griswaldbrooks/woodbike-shed/blender/renders/cam_back_right.png

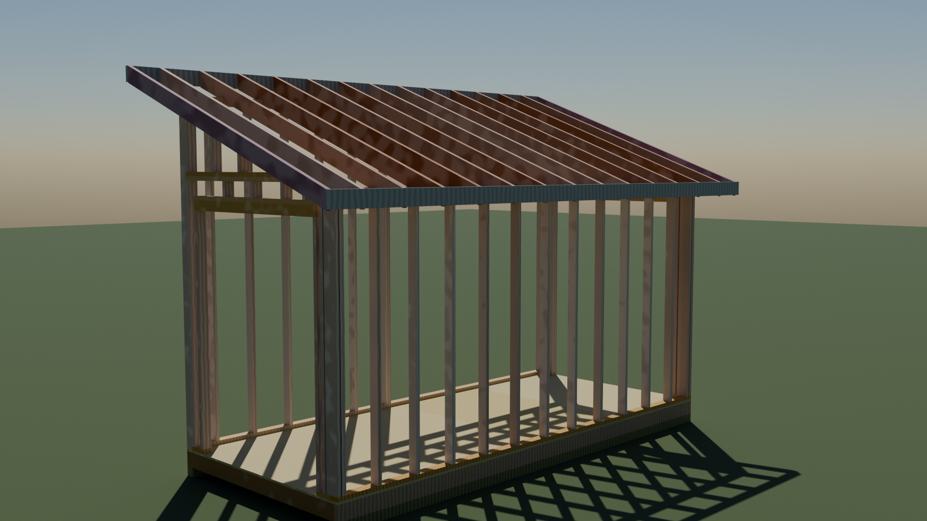
blender/renders/cam_back_right.png
