griswaldbrooks/woodbike-shed/blender/renders/cam_elevation.png

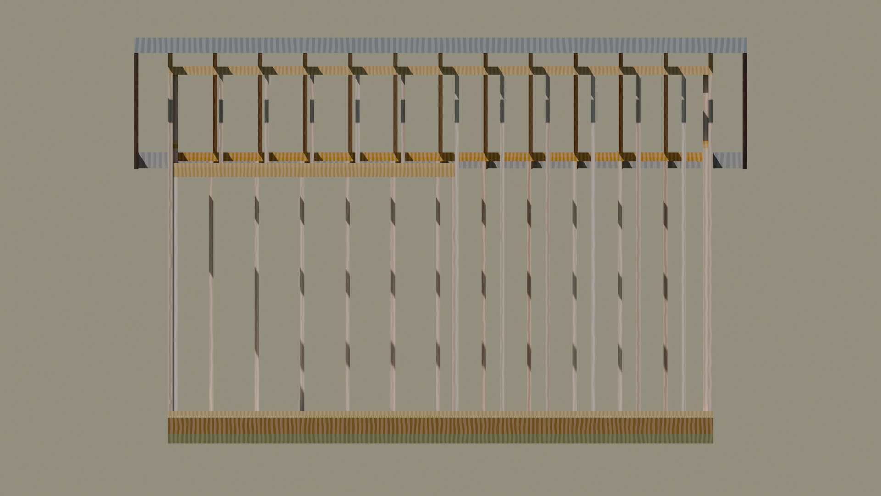
blender/renders/cam_elevation.png
