griswaldbrooks/woodbike-shed/blender/renders/cam_front_left.png

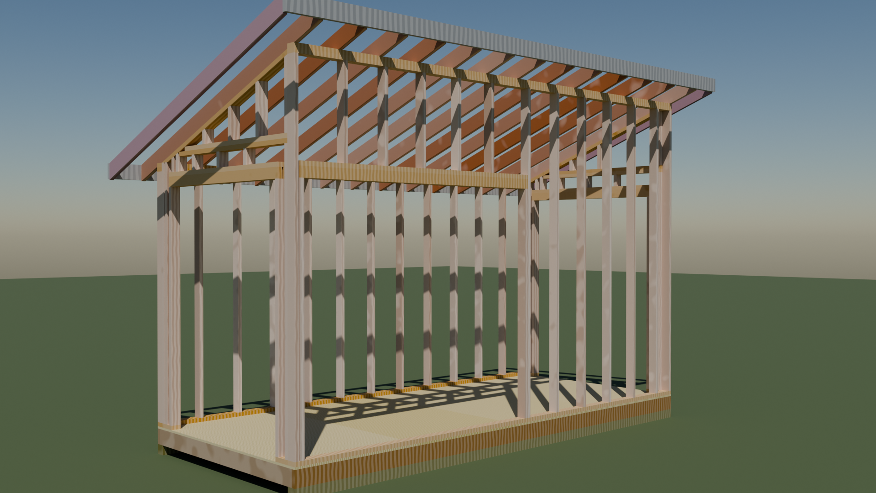
blender/renders/cam_front_left.png
