griswaldbrooks/woodbike-shed/blender/renders/skin/skin_back_right.png

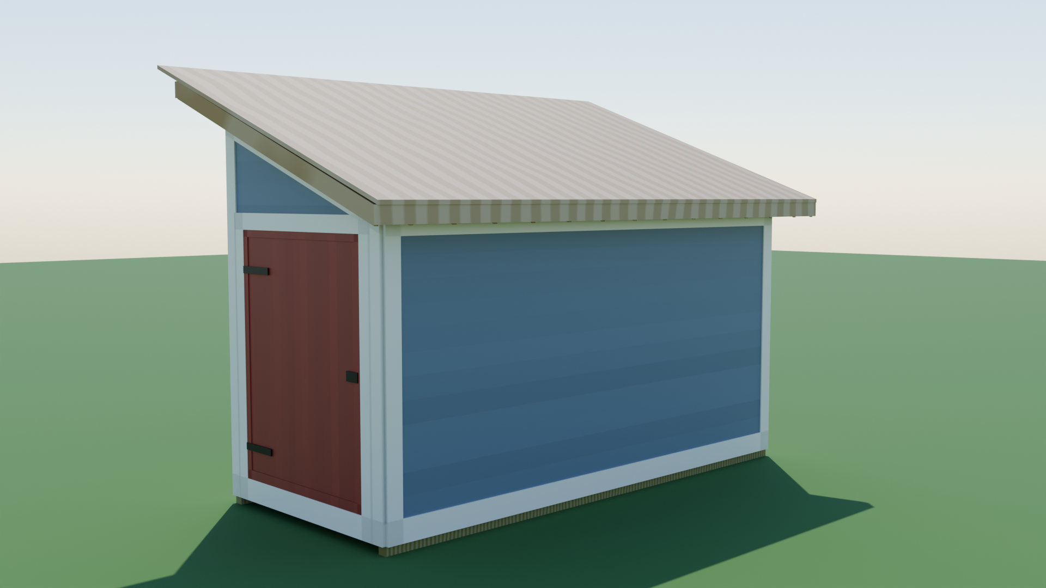
blender/renders/skin/skin_back_right.png
