griswaldbrooks/woodbike-shed/renders/shed-iso-back.png

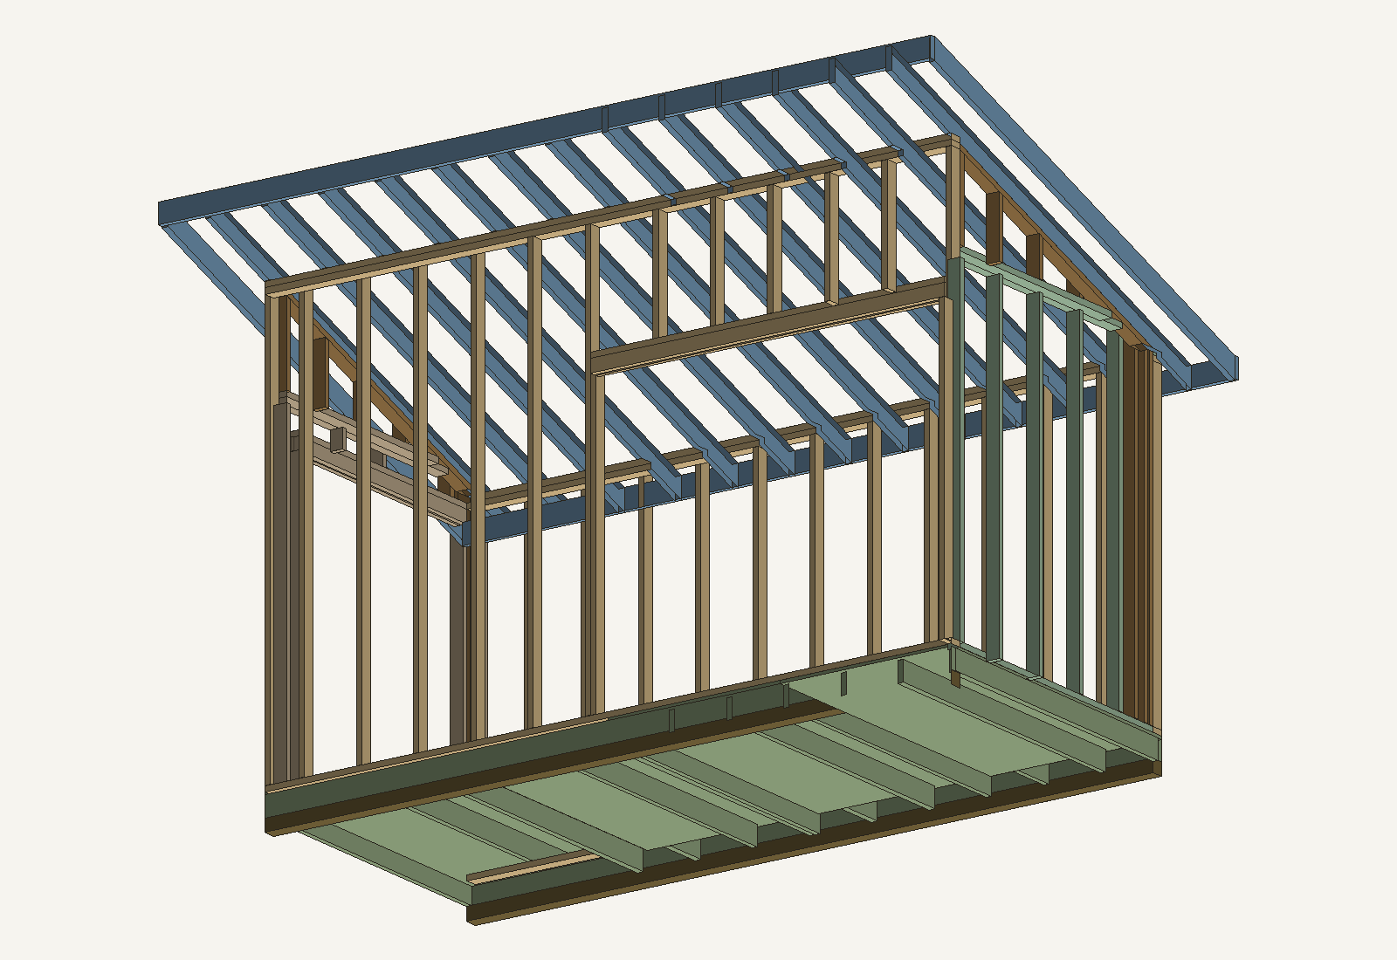
renders/shed-iso-back.png
