griswaldbrooks/woodbike-shed/renders/shed-side-right.png

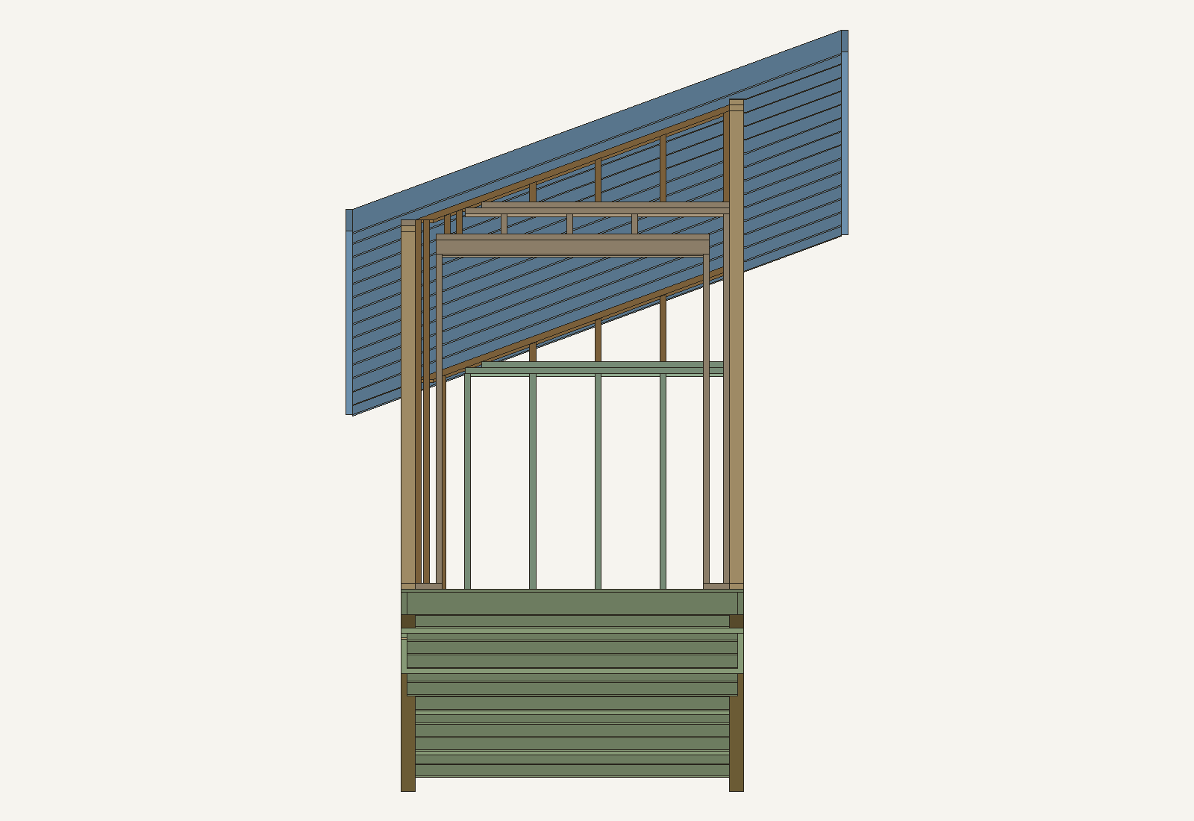
renders/shed-side-right.png
