griswaldbrooks/woodbike-shed/scripts/iso-winner2.png

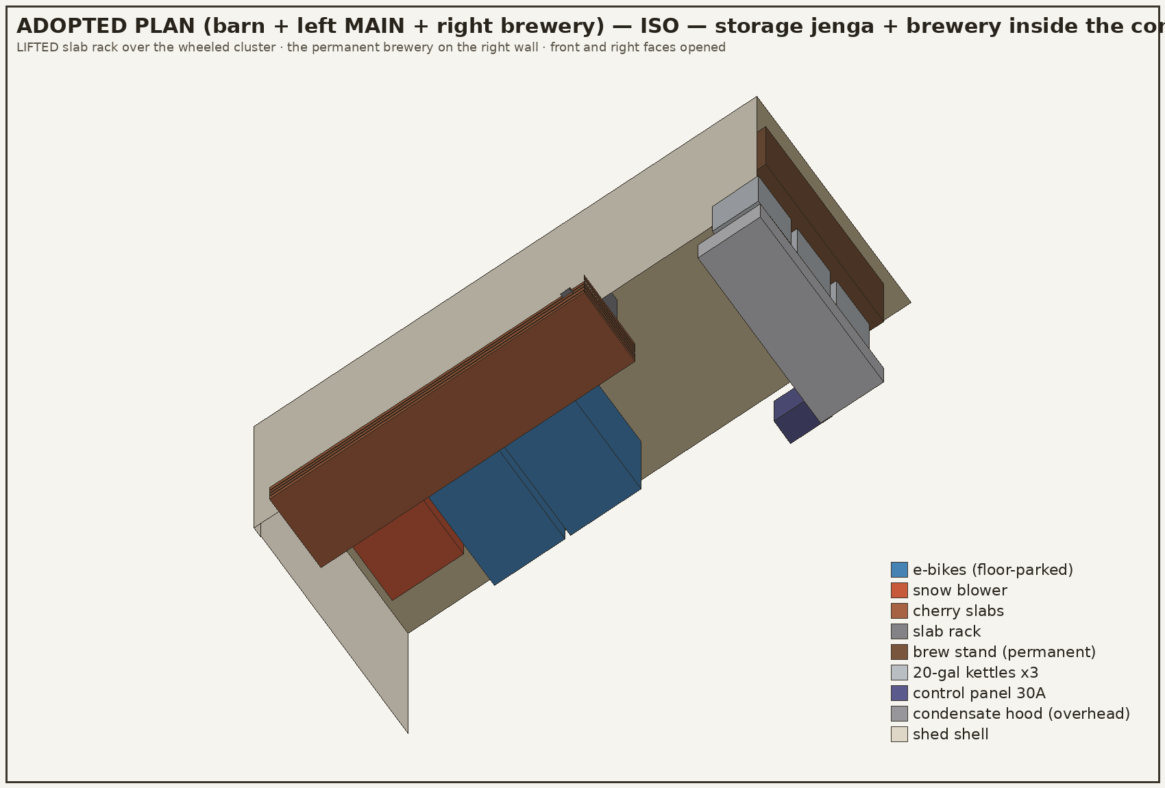
scripts/iso-winner2.png
