griswaldbrooks/woodbike-shed/scripts/plan-winner2.png

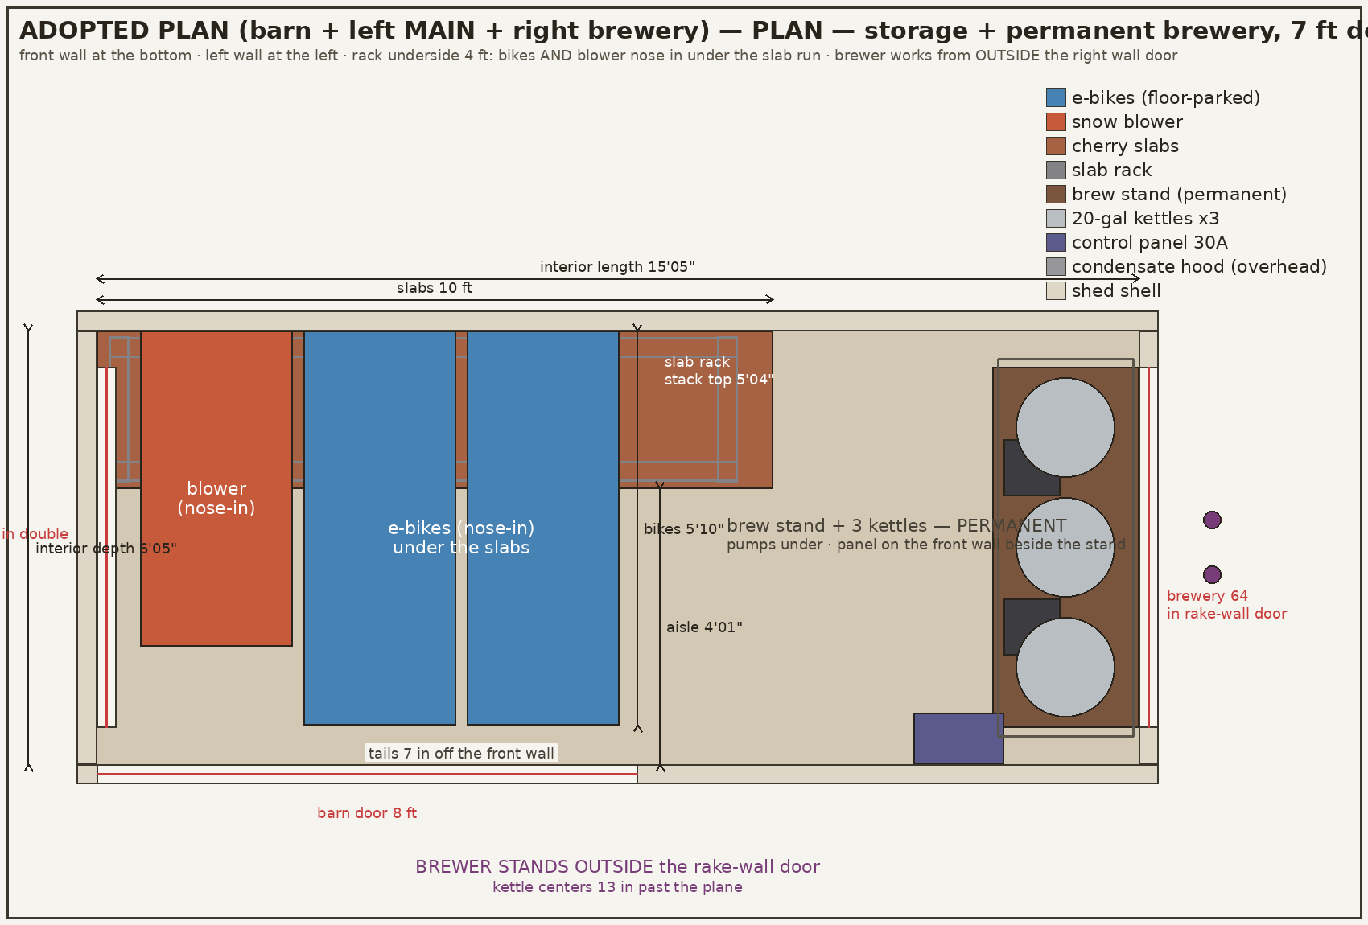
scripts/plan-winner2.png
