griswaldbrooks/woodbike-shed/scripts/section-winner2.png

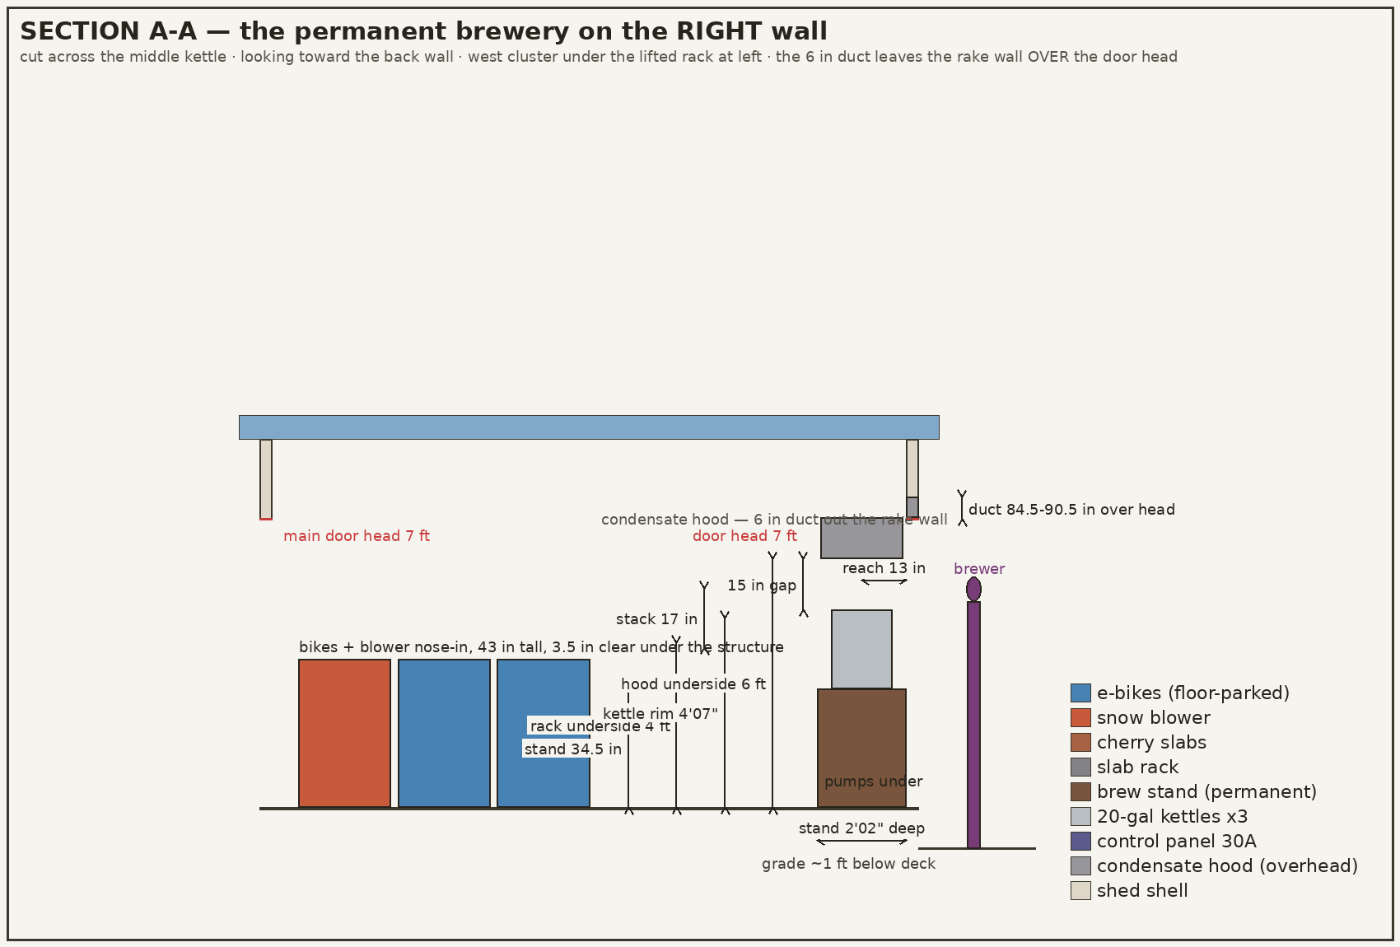
scripts/section-winner2.png
