griswaldbrooks/woodbike-shed/step/059 back wall double top plate short.step

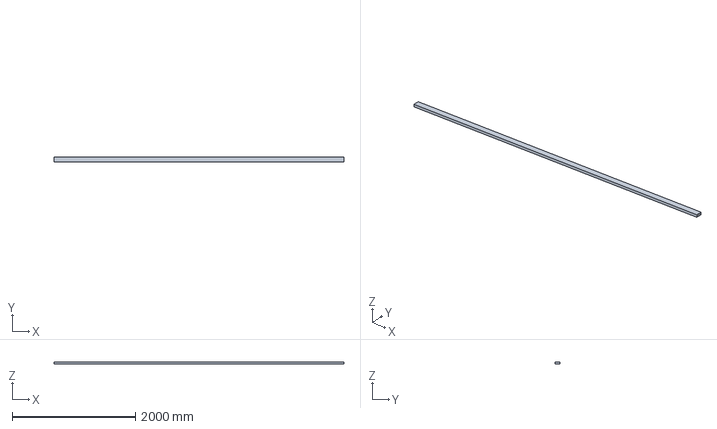
[picture p21: CAD file, 2026-08-24]
step/059 back wall double top plate short.step
4699.0 x 88.9 x 38.1 mm
