griswaldbrooks/woodbike-shed/step/054 back wall studs.step

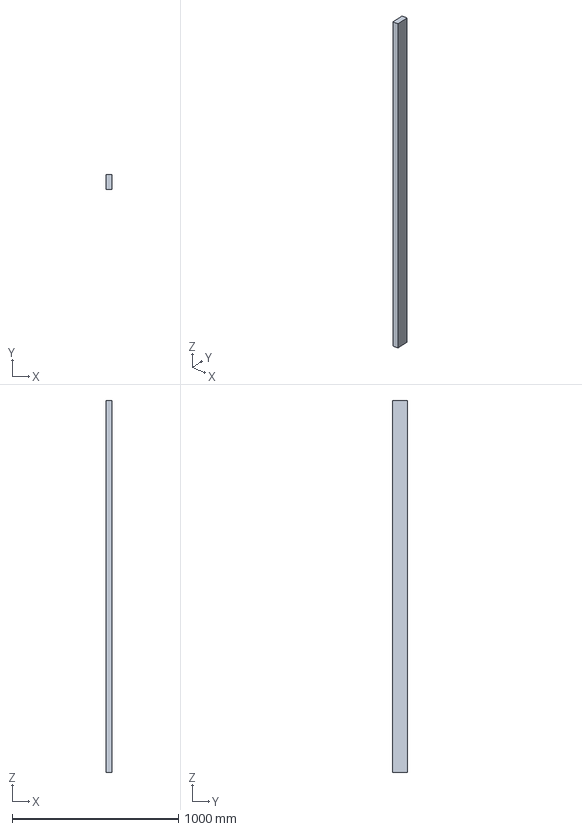
[picture p22: CAD file, 2026-08-24]
step/054 back wall studs.step
38.1 x 88.9 x 2238.4 mm
