griswaldbrooks/woodbike-shed/step/013 floor joist.step

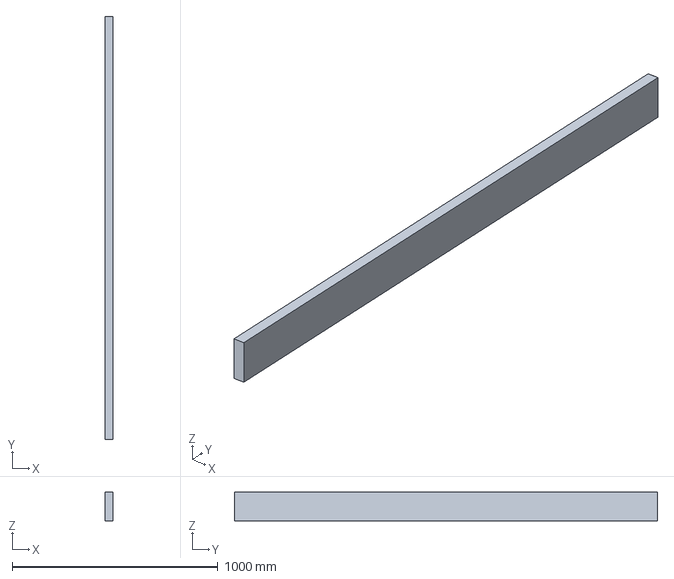
[picture p23: CAD file, 2026-08-24]
step/013 floor joist.step
38.1 x 2057.4 x 139.7 mm
