griswaldbrooks/woodbike-shed/step/275 finish door rails.step

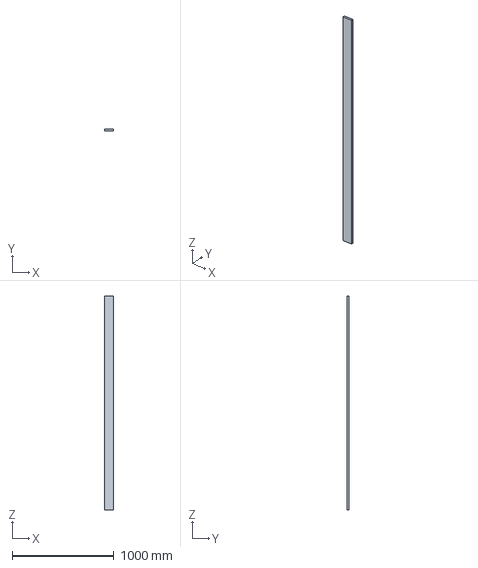
[picture p24: CAD file, 2026-08-24]
step/275 finish door rails.step
88.9 x 19.1 x 2101.8 mm
