griswaldbrooks/woodbike-shed/step/040 front wall cripple studs.step

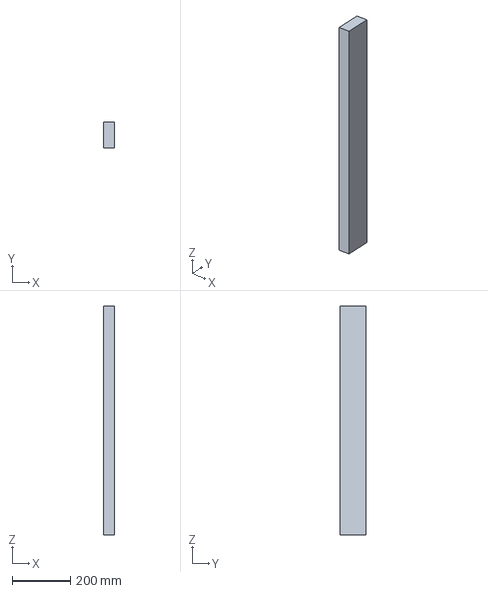
[picture p25: CAD file, 2026-08-24]
step/040 front wall cripple studs.step
38.1 x 88.9 x 787.4 mm
