griswaldbrooks/woodbike-shed/step/037 front wall headers.step

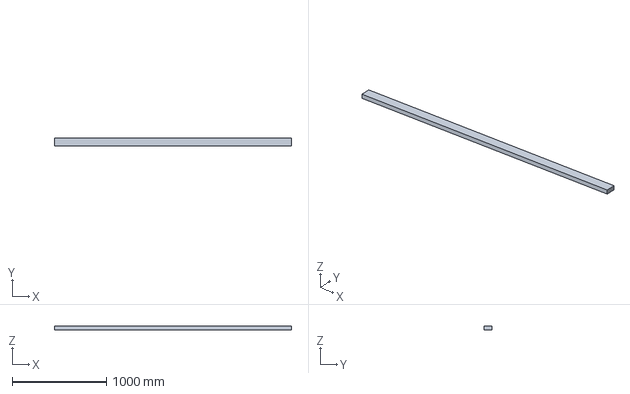
[picture p26: CAD file, 2026-08-24]
step/037 front wall headers.step
2514.6 x 88.9 x 38.1 mm
