griswaldbrooks/woodbike-shed/step/128 finish siding front.step

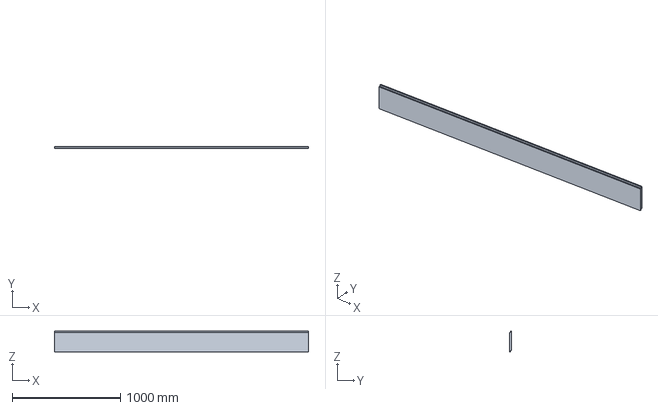
[picture p27: CAD file, 2026-08-24]
step/128 finish siding front.step
2349.5 x 19.0 x 190.5 mm
