griswaldbrooks/woodbike-shed/step/107 right rake wall top plate.step

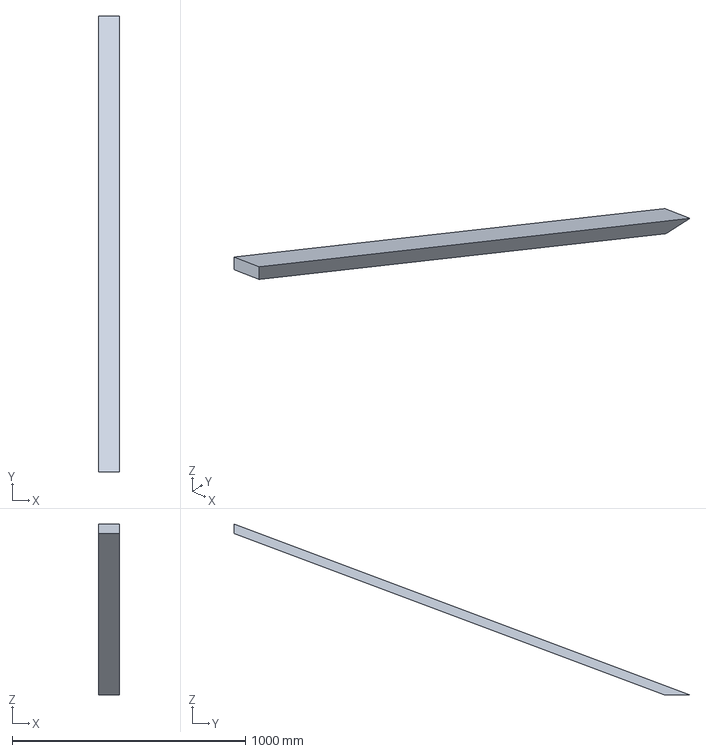
[picture p28: CAD file, 2026-08-24]
step/107 right rake wall top plate.step
88.9 x 1955.8 x 733.4 mm
