griswaldbrooks/woodbike-shed/step/311 finish door planks.step

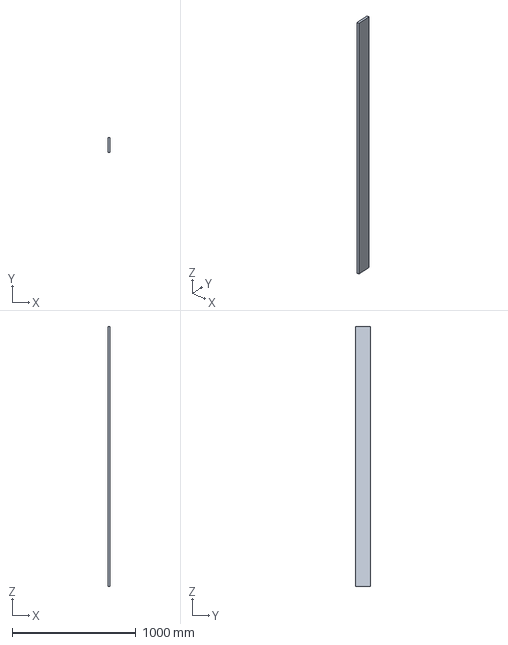
[picture p29: CAD file, 2026-08-24]
step/311 finish door planks.step
19.0 x 121.1 x 2101.8 mm
