griswaldbrooks/woodbike-shed/step/164 finish siding back.step

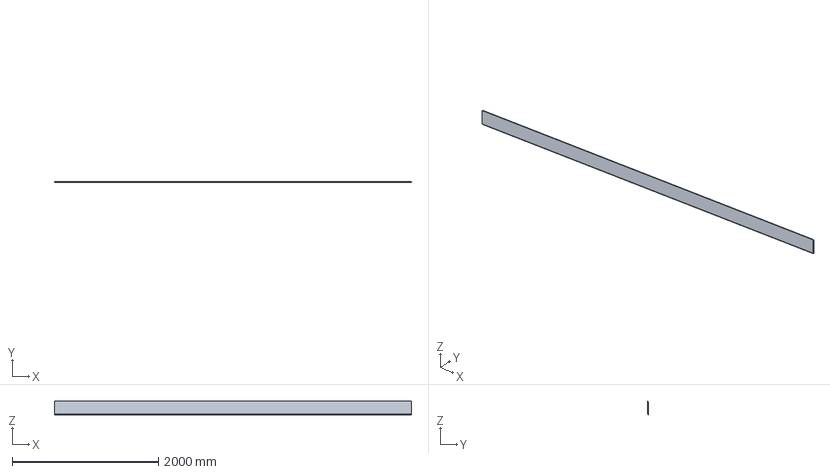
[picture p30: CAD file, 2026-08-24]
step/164 finish siding back.step
4876.8 x 19.0 x 190.5 mm
