griswaldbrooks/woodbike-shed/step/094 left rake wall studs.step

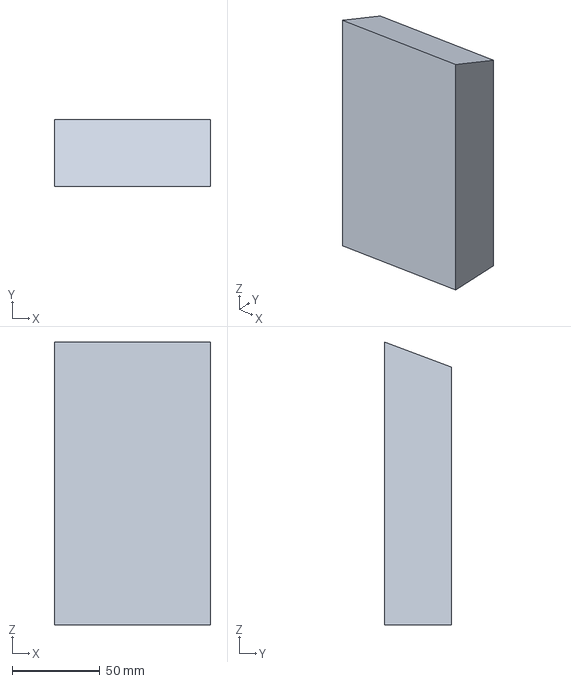
[picture p31: CAD file, 2026-08-24]
step/094 left rake wall studs.step
88.9 x 38.1 x 160.9 mm
