griswaldbrooks/woodbike-shed/step/062 left wall bottom plate long.step

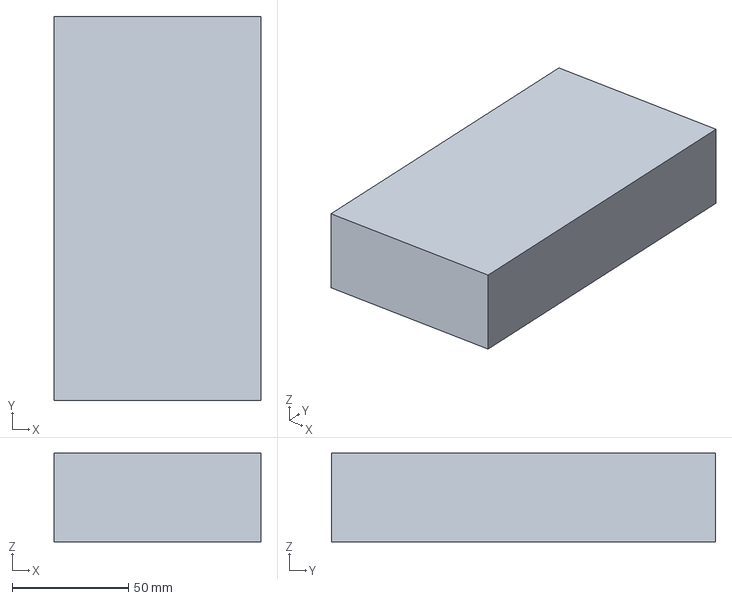
[picture p32: CAD file, 2026-08-24]
step/062 left wall bottom plate long.step
88.9 x 165.1 x 38.1 mm
