griswaldbrooks/woodbike-shed/step/256 finish door planks.step

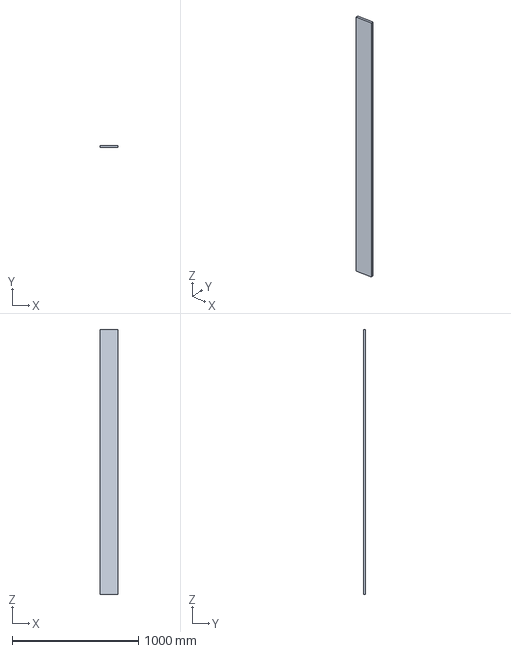
[picture p33: CAD file, 2026-08-24]
step/256 finish door planks.step
139.3 x 19.1 x 2101.8 mm
