griswaldbrooks/woodbike-shed/step/175 finish siding left.step

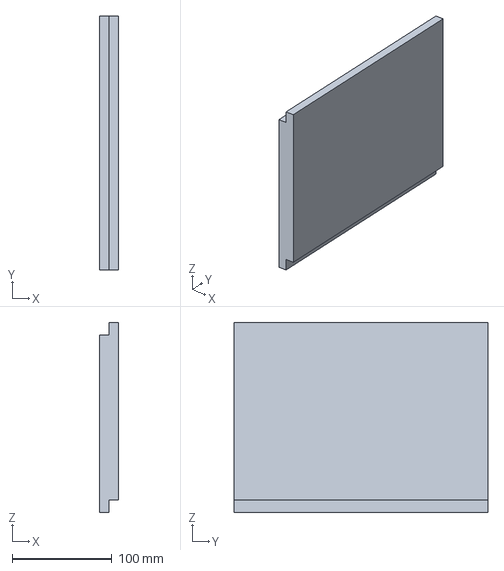
[picture p34: CAD file, 2026-08-24]
step/175 finish siding left.step
19.0 x 254.0 x 190.5 mm
