griswaldbrooks/woodbike-shed/step/310 finish door rails.step

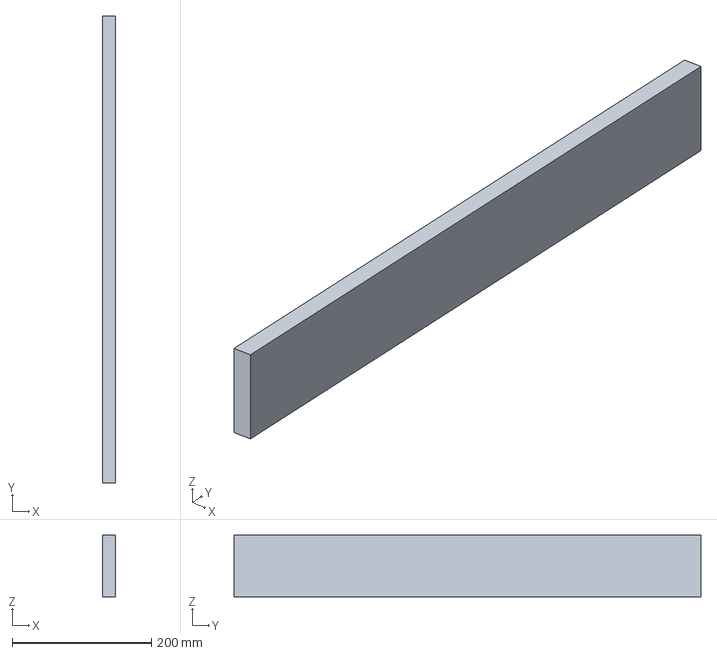
[picture p35: CAD file, 2026-08-24]
step/310 finish door rails.step
19.0 x 669.9 x 88.9 mm
