griswaldbrooks/woodbike-shed/step/246 finish door casings.step

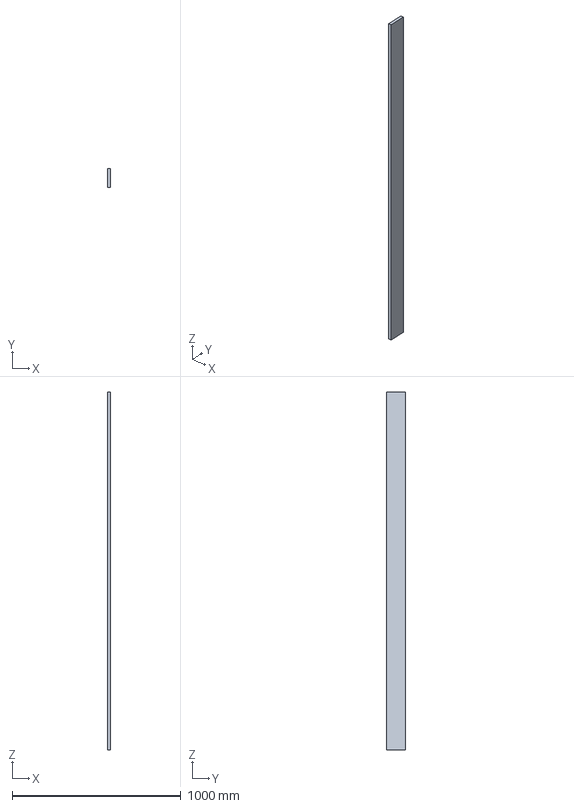
[picture p36: CAD file, 2026-08-24]
step/246 finish door casings.step
19.1 x 114.3 x 2120.9 mm
