griswaldbrooks/woodbike-shed/step/234 finish corner boards.step

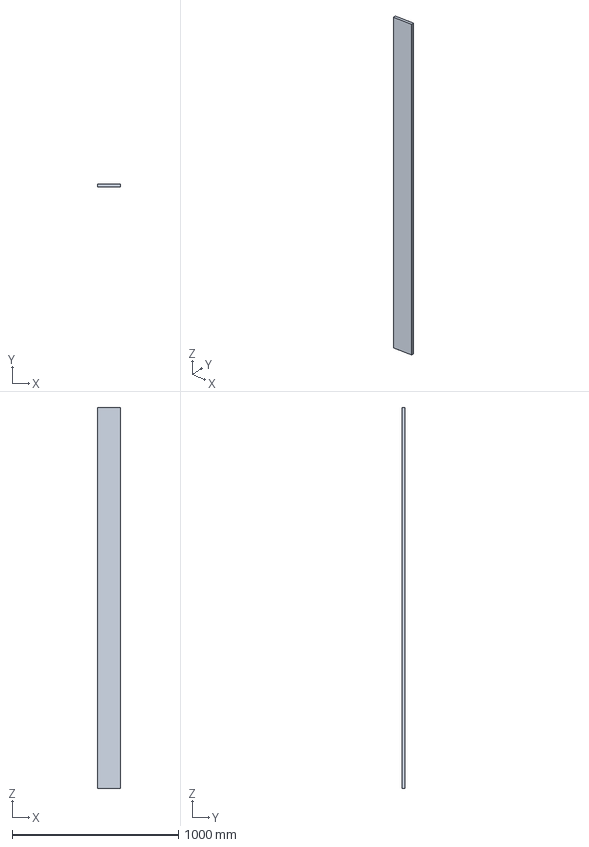
[picture p37: CAD file, 2026-08-24]
step/234 finish corner boards.step
139.7 x 19.1 x 2292.4 mm
