griswaldbrooks/woodbike-shed/step/193 finish siding left.step

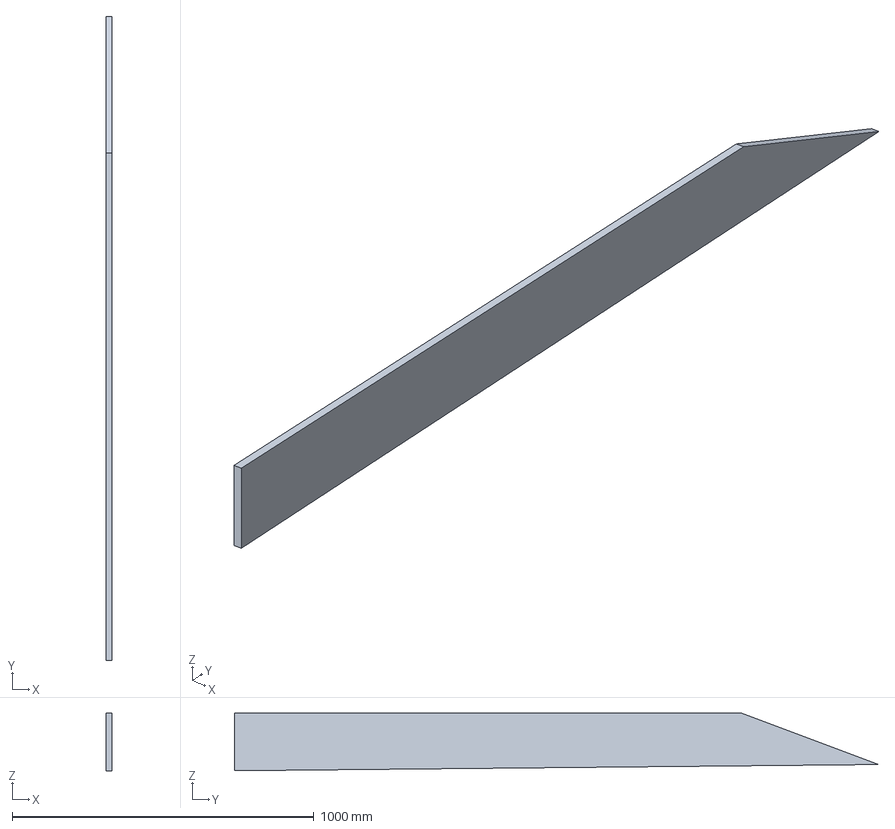
[picture p38: CAD file, 2026-08-24]
step/193 finish siding left.step
19.0 x 2133.6 x 190.5 mm
