griswaldbrooks/woodbike-shed/step/034 front wall jack studs.step

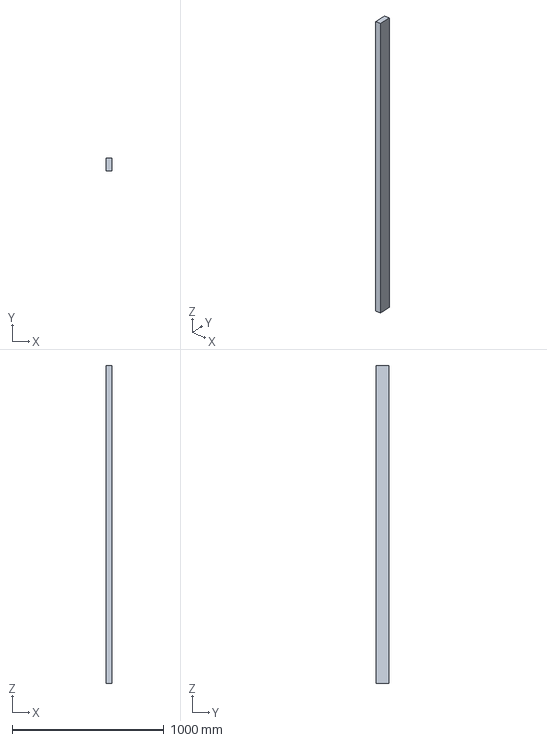
[picture p39: CAD file, 2026-08-24]
step/034 front wall jack studs.step
38.1 x 88.9 x 2095.5 mm
