griswaldbrooks/woodbike-shed/step/089 right wall cripple studs.step

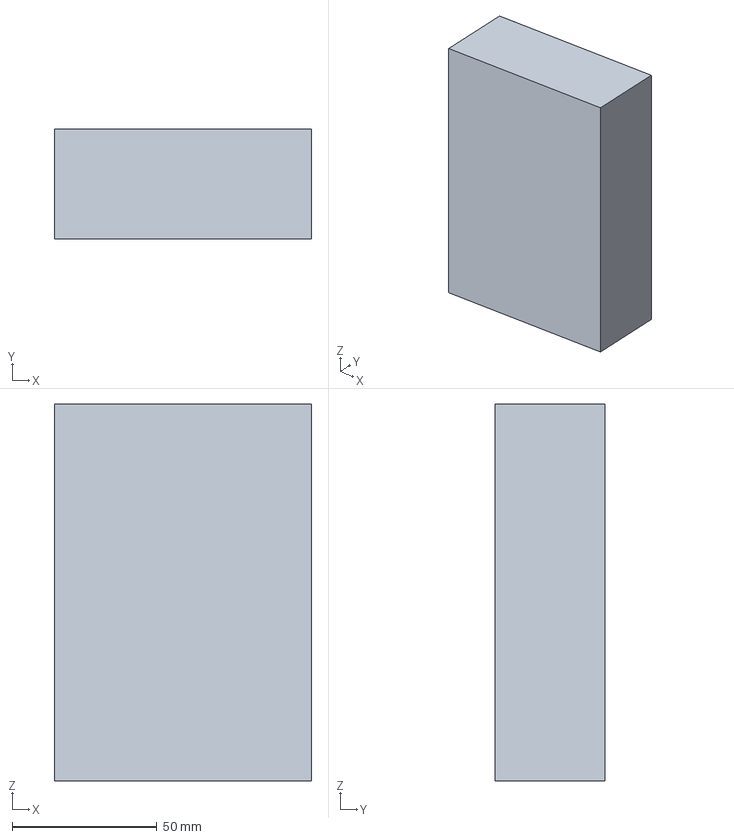
[picture p40: CAD file, 2026-08-24]
step/089 right wall cripple studs.step
88.9 x 38.1 x 130.2 mm
