griswaldbrooks/woodbike-shed/step/026 front wall king studs.step

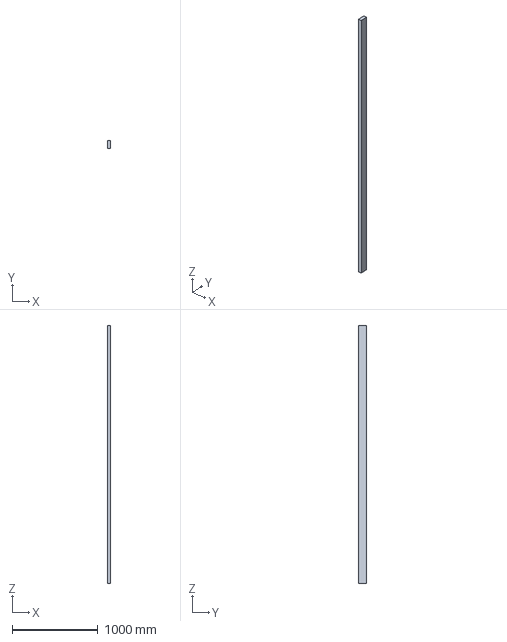
[picture p41: CAD file, 2026-08-24]
step/026 front wall king studs.step
38.1 x 88.9 x 3009.9 mm
