griswaldbrooks/woodbike-shed/step/251 finish door casings.step

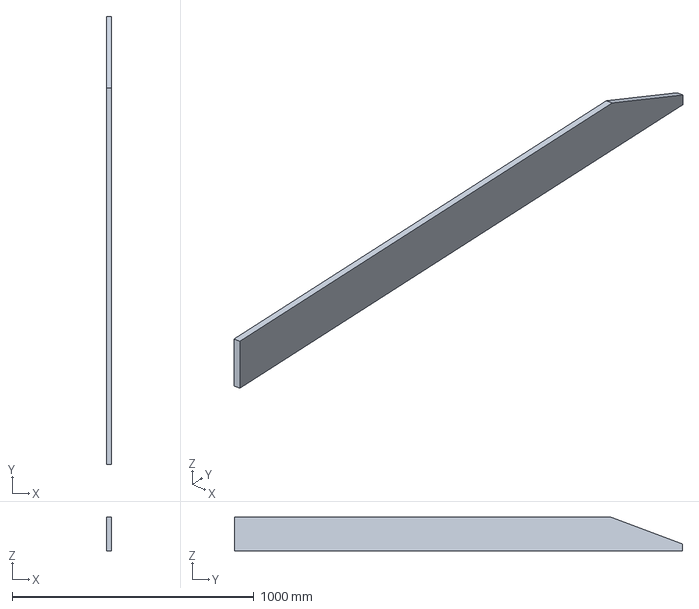
[picture p42: CAD file, 2026-08-24]
step/251 finish door casings.step
19.1 x 1854.2 x 139.7 mm
