griswaldbrooks/woodbike-shed/step/031 front wall bottom plate.step

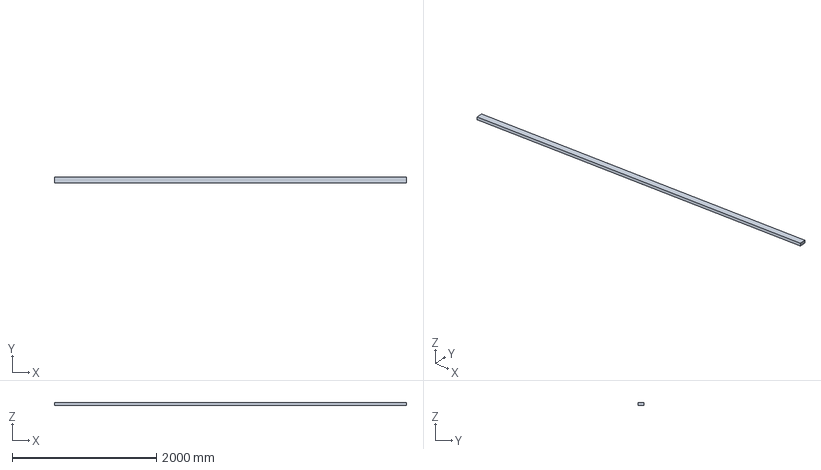
[picture p43: CAD file, 2026-08-24]
step/031 front wall bottom plate.step
4876.8 x 88.9 x 38.1 mm
