griswaldbrooks/woodbike-shed/step/065 left wall double top plate.step

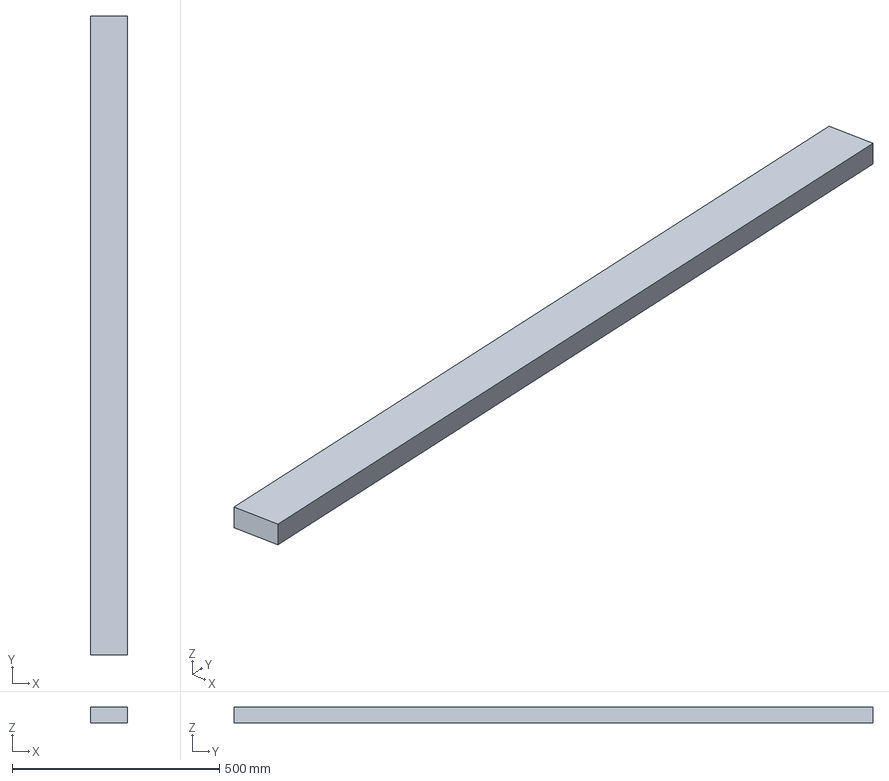
[picture p44: CAD file, 2026-08-24]
step/065 left wall double top plate.step
88.9 x 1542.5 x 38.1 mm
