griswaldbrooks/woodbike-shed/step/232 finish corner boards.step

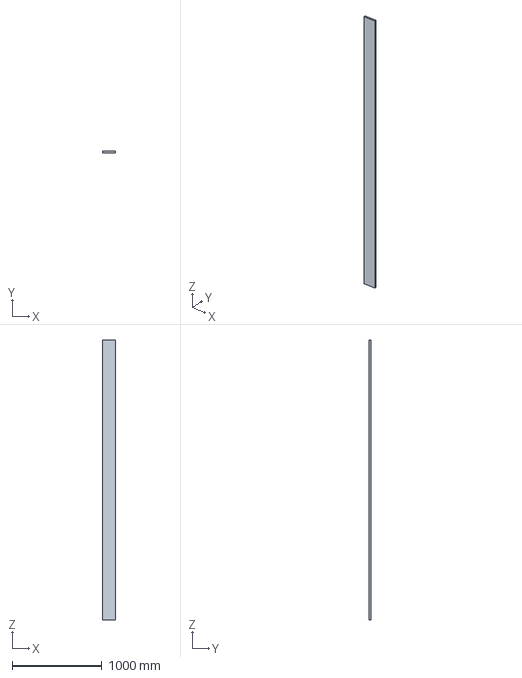
[picture p45: CAD file, 2026-08-24]
step/232 finish corner boards.step
139.7 x 19.1 x 3111.5 mm
