griswaldbrooks/woodbike-shed/step/231 finish skirt.step

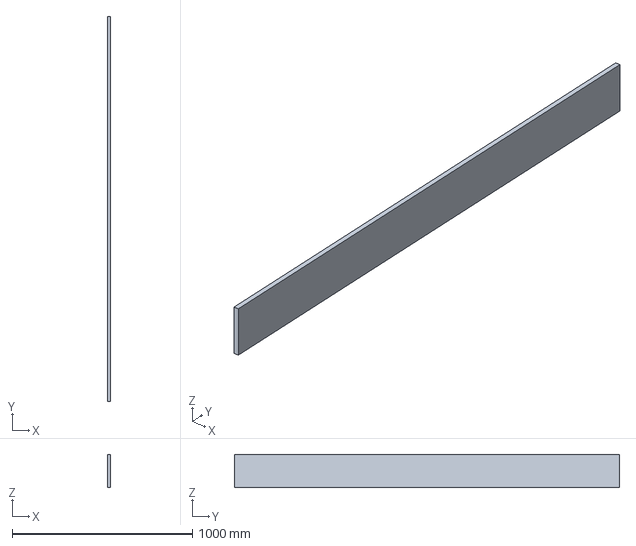
[picture p46: CAD file, 2026-08-24]
step/231 finish skirt.step
19.0 x 2133.6 x 184.1 mm
