griswaldbrooks/woodbike-shed/step/194 finish siding left.step

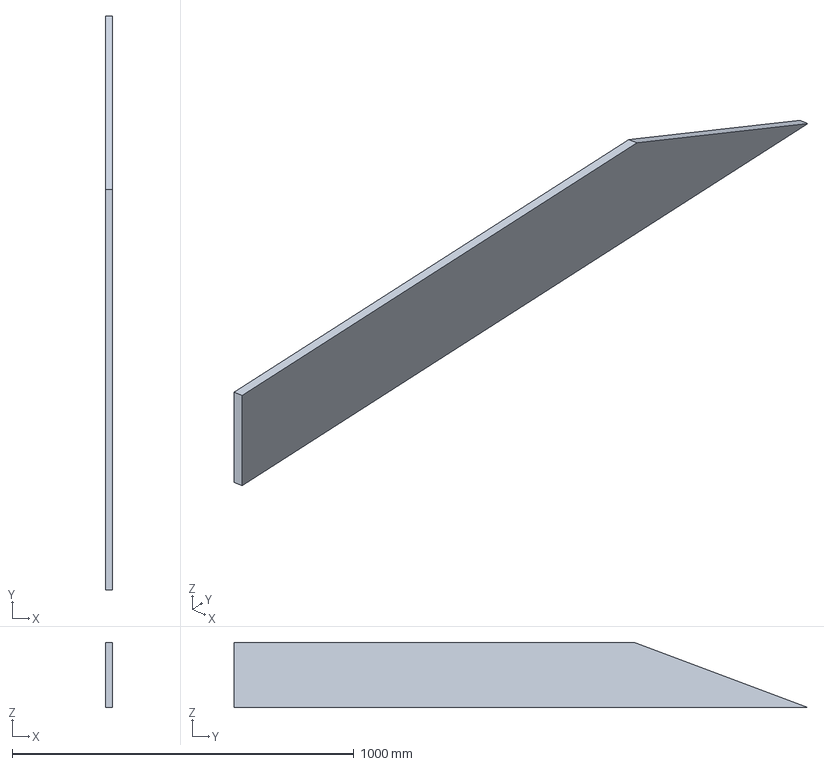
[picture p47: CAD file, 2026-08-24]
step/194 finish siding left.step
19.0 x 1680.6 x 190.5 mm
