griswaldbrooks/woodbike-shed/step/226 finish siding right.step

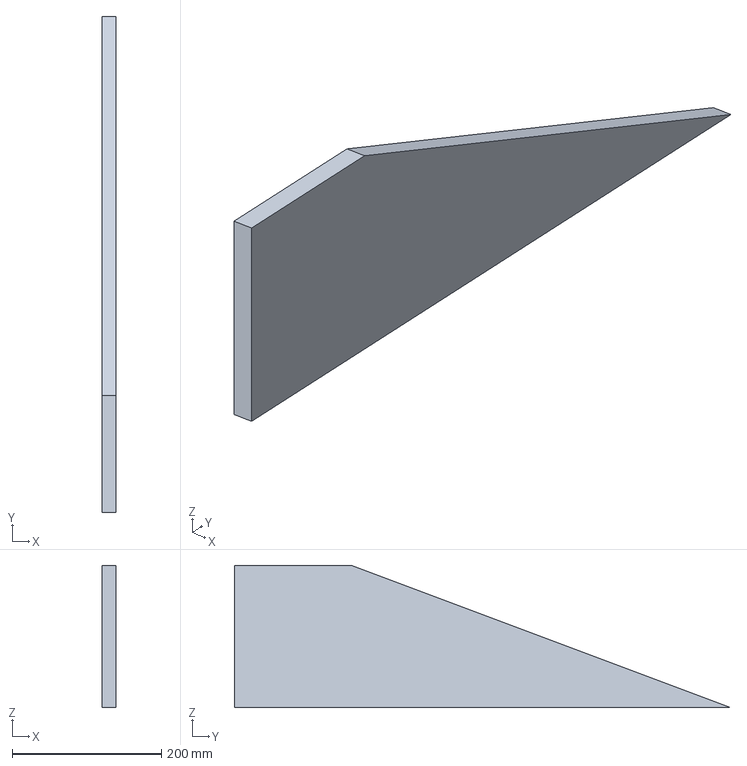
[picture p48: CAD file, 2026-08-24]
step/226 finish siding right.step
19.1 x 664.6 x 190.5 mm
