griswaldbrooks/woodbike-shed/step/084 right wall headers.step

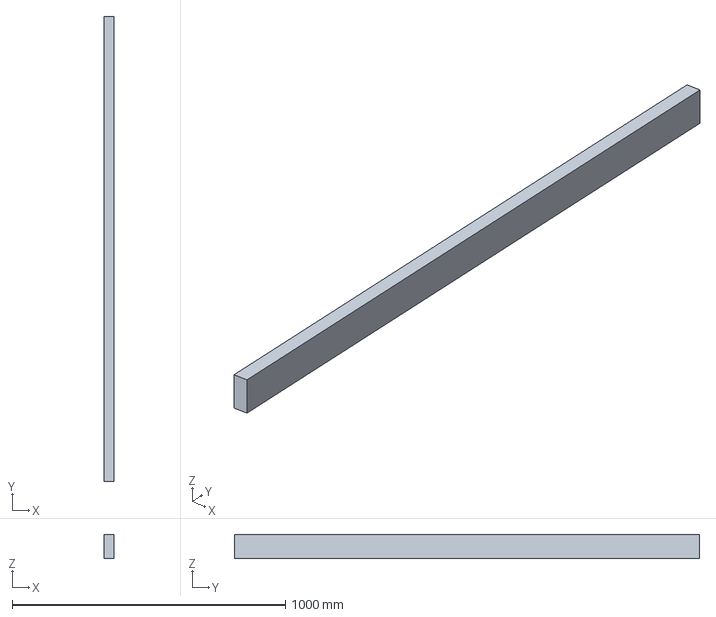
[picture p49: CAD file, 2026-08-24]
step/084 right wall headers.step
38.1 x 1701.8 x 88.9 mm
