griswaldbrooks/woodbike-shed/step/228 finish skirt.step

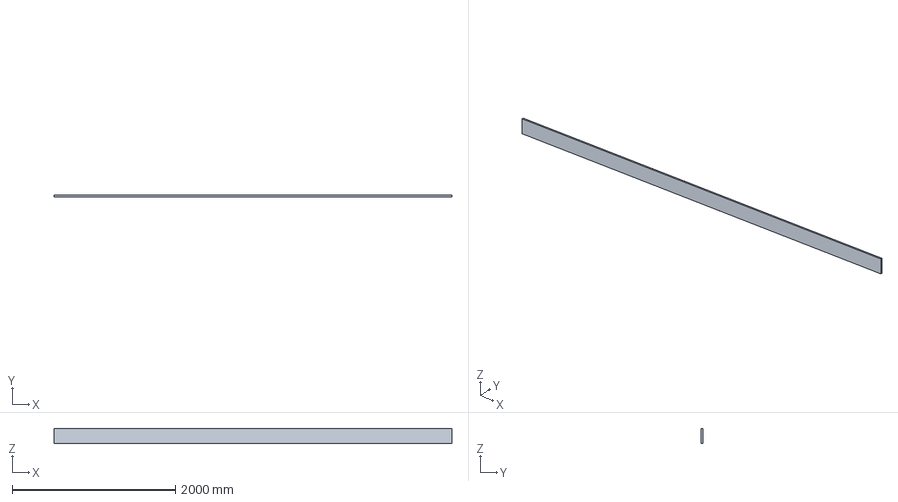
[picture p50: CAD file, 2026-08-24]
step/228 finish skirt.step
4876.8 x 19.1 x 184.1 mm
