griswaldbrooks/woodbike-shed/step/003 rim joist.step

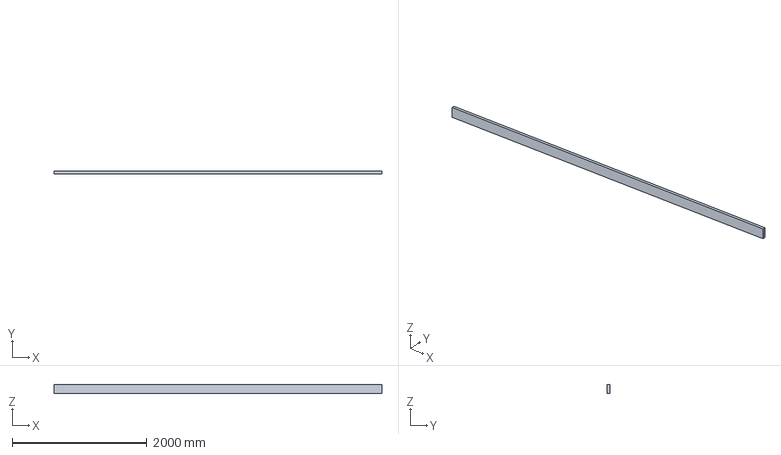
[picture p51: CAD file, 2026-08-24]
step/003 rim joist.step
4876.8 x 38.1 x 139.7 mm
