griswaldbrooks/woodbike-shed/step/099 right rake wall studs.step

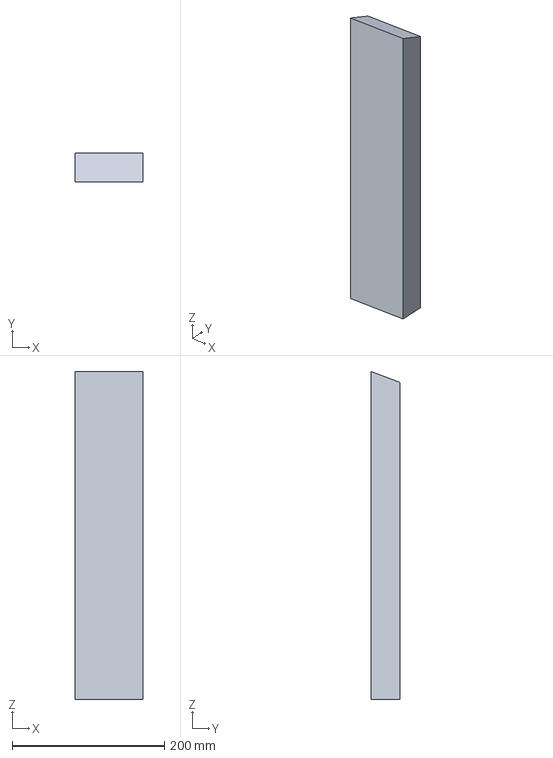
[picture p52: CAD file, 2026-08-24]
step/099 right rake wall studs.step
88.9 x 38.1 x 430.8 mm
