griswaldbrooks/woodbike-shed/step/225 finish siding right.step

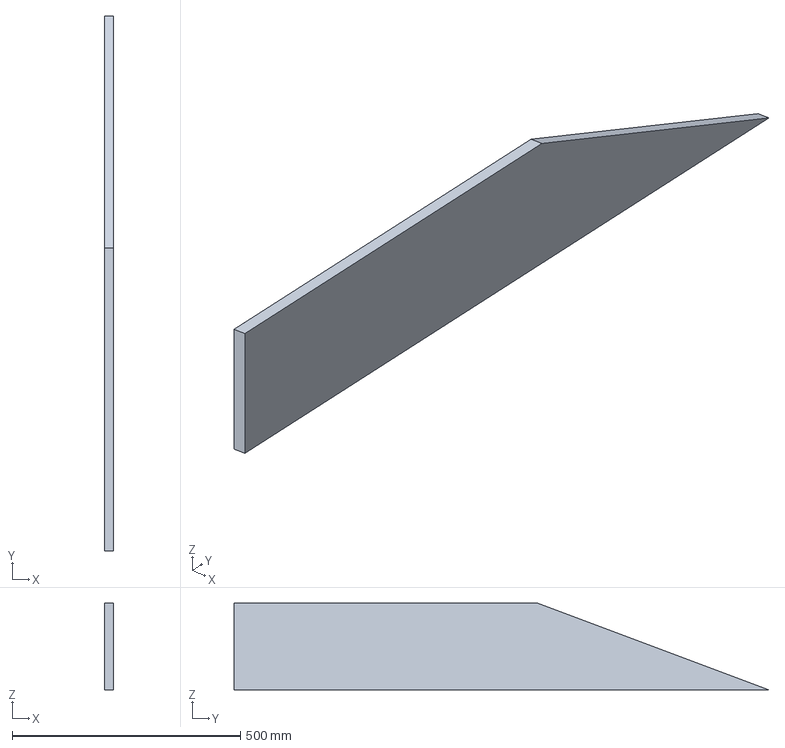
[picture p53: CAD file, 2026-08-24]
step/225 finish siding right.step
19.1 x 1172.6 x 190.5 mm
