griswaldbrooks/woodbike-shed/step/081 right wall double top plate.step

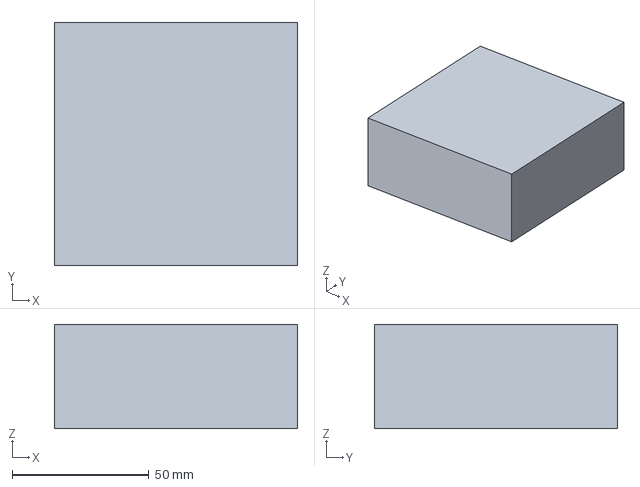
[picture p54: CAD file, 2026-08-24]
step/081 right wall double top plate.step
88.9 x 88.9 x 38.1 mm
