griswaldbrooks/woodbike-shed/step/192 finish siding left.step

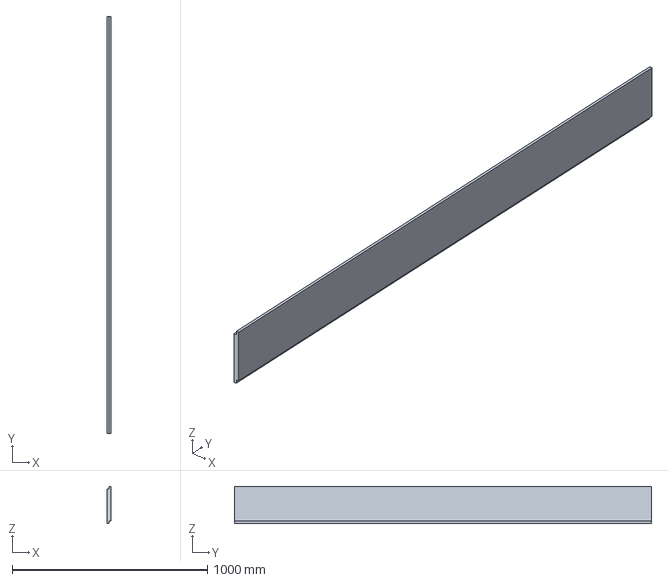
[picture p55: CAD file, 2026-08-24]
step/192 finish siding left.step
19.0 x 2133.6 x 190.5 mm
