griswaldbrooks/woodbike-shed/step/242 finish frieze.step

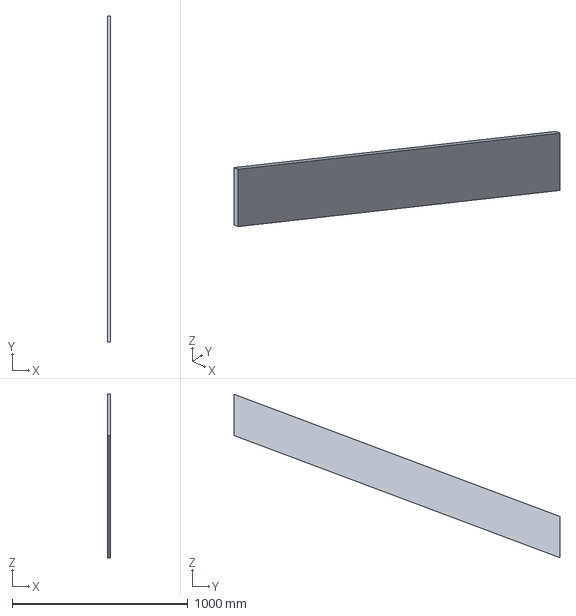
[picture p56: CAD file, 2026-08-24]
step/242 finish frieze.step
19.0 x 1854.2 x 930.3 mm
