griswaldbrooks/woodbike-shed/step/167 finish siding back.step

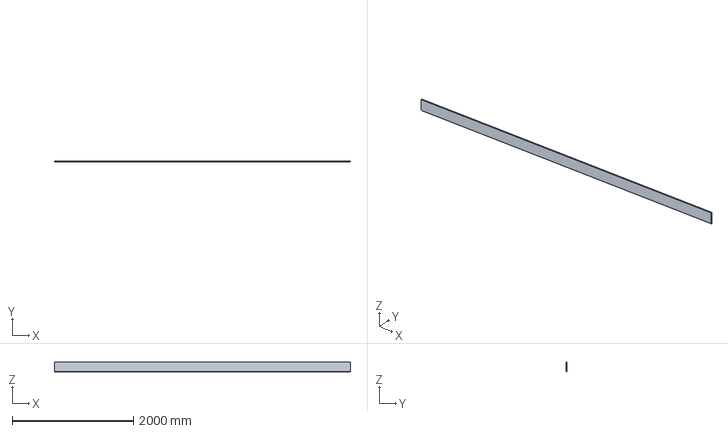
[picture p57: CAD file, 2026-08-24]
step/167 finish siding back.step
4876.8 x 19.0 x 171.5 mm
