griswaldbrooks/woodbike-shed/step/020 sub floor osb.step

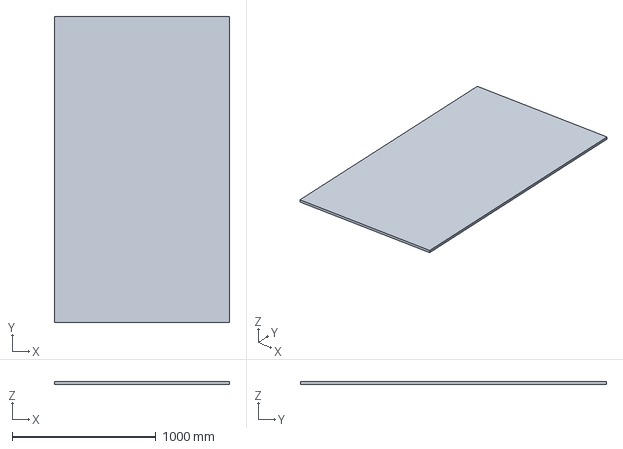
[picture p58: CAD file, 2026-08-24]
step/020 sub floor osb.step
1219.2 x 2133.6 x 19.1 mm
