griswaldbrooks/woodbike-shed/step/101 right rake wall studs.step

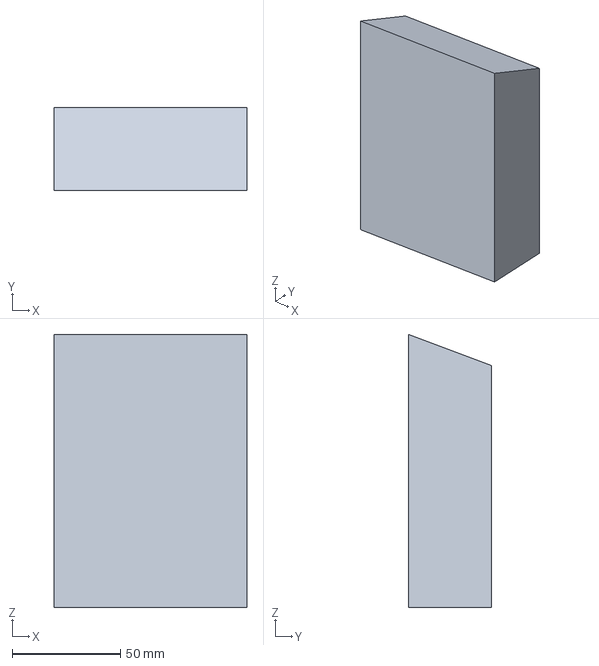
[picture p59: CAD file, 2026-08-24]
step/101 right rake wall studs.step
88.9 x 38.1 x 126.0 mm
