griswaldbrooks/woodbike-shed/step/240 finish frieze.step

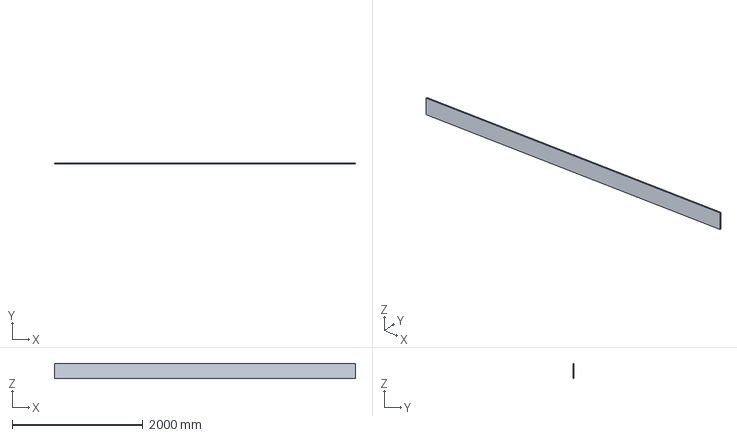
[picture p60: CAD file, 2026-08-24]
step/240 finish frieze.step
4597.4 x 19.1 x 234.9 mm
