griswaldbrooks/woodbike-shed/step/244 finish door casings.step

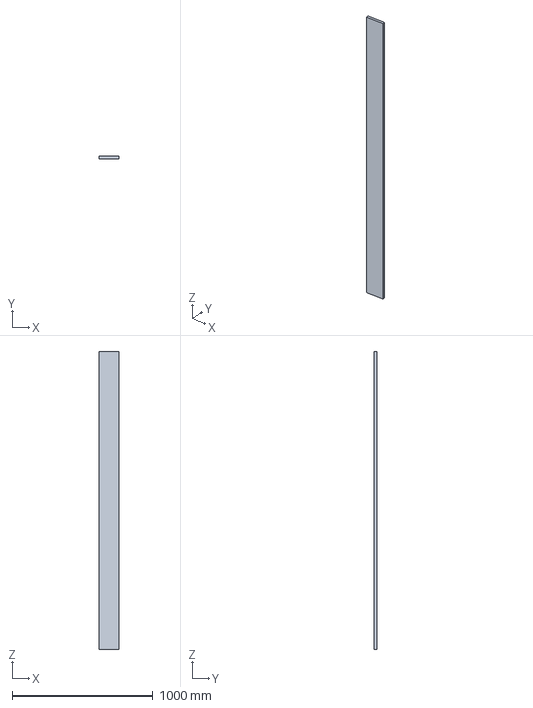
[picture p61: CAD file, 2026-08-24]
step/244 finish door casings.step
139.7 x 19.1 x 2120.9 mm
