griswaldbrooks/woodbike-shed/docs/build-guide.html

# Wood Bike Shed — Project Overview & Step-by-Step Build Guide

Regenerated 2026-08-11 from the landed model code (repo woodbike-shed, commit c86e75d). Replaces the Onshape-era design report (archived alongside as report.2026-08-08.onshape.html).

ARCHIVED 2026-08-13 — do not build from this page. It records the retired 6 ft design (old door plan, block foundation, the old front roof overhang). The current guide is the multi-page guide in docs/guide/: 16 ft × 7 ft shell, roof overhanging 12" on all four sides.

This document supersedes the Onshape-era report. Every dimension and count below is derived from the build123d model-as-code in cad/*.py and its generated cut lists (CUT_LIST.md, order_list.csv, order_list_finish.csv) — the ONLY geometry authorities. The Onshape document is a retired record copy that still carries stale numbers (93" studs, sistered skids, no birdsmouths, no finish parts). Do not take any measurement from it. Model state verified on 2026-08-11: cad.verify → OK: 293 parts (117 framing, 176 finish), 0 unallowed interference.

Contents

1. Project overview
2. Materials and ordering (framing order + finish order, kept separate)
3. Step-by-step build guide
  1. Stage 1 — Foundation, skids, floor
  2. Stage 2 — Walls: 2A front · 2B back · 2C left rake wall · 2D right rake wall
  3. Stage 3 — Roof (rake plates, birdmouthed rafters, fascia/rake boards, roofing)
  4. Stage 4 — Finish (lap siding, trim, board-and-batten doors)
4. Cut list reference
5. Sources, verification, known quirks

## 1. Project overview

One combined wood shed + bike shed: a 16 ft × 6 ft rectangular box with a single-slope (shed) roof, the tall wall at the front (door) side, three exterior door openings, lap siding, and board-and-batten doors. It rides on two continuous pressure-treated 4×4 skids bearing on eight Tuff Blocks set in gravel pockets — no concrete foundation.

Overall | Value (as modeled)
Framed footprint (wall outer faces) | 192" × 72" (16' × 6'), x −3.5…188.5 × y −3.5…68.5 in model coords
Roof plan incl. overhangs | 216" × 111" (18' × 9'‑3") — 12" gable-end overhangs to the fascia faces, 24" front overhang, 12" back overhang
Deck top | z = 0; platform sits ~9¾" above the skid bottoms (z = −9.75")
Wall heights (deck → plate tops) | front wall 123" (10'‑3"); back/left/right walls 97⅛" (92⅝" pre-cut studs + 3 plates)
Roof pitch | 4.5 : 12 (24.375/65, 20.56°), derived from the plate solids; high side at the front
Peak height | 137‑11/16" above deck at the front fascia top
Door openings (rough, framed) | front: one 36" × 84" + one 72" × 84" (double); right wall: one 36" × 84"
Framing parts / finish parts | 117 framing parts in 36 cut-list groups; 176 finish parts (siding/trim/doors)

### Key design decisions (plain language)

- 92‑5/8" pre-cut studs. Back, left and right walls use standard pre-cut studs; the wall height is 97⅛" (was 97½" with the old 93" studs). The roof was re-derived about the unchanged front wall, moving the pitch from 24/65 to 24.375/65.
- Two continuous 16‑ft 4×4 skids. No sistering, no splices: one PT 4×4 per skid line, full shed length, under the front and back wall bearing lines. Hingham Lumber stocks 16' 4×4s.
- Birdmouth-seated rafters. Every one of the 13 rafters carries a front birdsmouth (flat seat on the front double top plate top at z = 123", heel 4" outboard of the wall inner face) and a back seat on the back double top plate top (z = 97⅛"), so the rafters bear flush on both plates instead of interpenetrating them.
- SPF #2 kiln-dried framing. All wall and roof lumber is KD SPF #2. Pressure-treated lumber (ground-contact rated, skids + entire floor system) is whatever Hingham Lumber stocks — the species is not ours to choose.
- Board-and-batten doors. Four leaves (one single + one center double on the front wall, one single on the right wall): vertical 1×6 planks with a 1×4 perimeter frame, hung on the casing face with 12" strap hinges.
- 1×8 lap (drop) siding, 7" exposure. Rabbet-nested courses keep the wall in one plane; no separate structural sheathing is modeled — the siding is the wall surface.
- Two separate order lists. Framing lumber and finish lumber (siding/trim/doors/hardware) are ordered as completely separate orders — never merged. Quantities are EXACT (no waste factor); shortages get a follow-up run.

Fig. 1 — Overall cross-section. Front wall plate top 123", back/left/right plate tops 97⅛", deck at z = 0, rafters birdmouthed onto both double top plates. 16' × 6' framed footprint.

## 2. Materials and ordering

Yard: Hingham Lumber. KD framing species is SPF #2; the yard stocks 16' 2×4, 16' 4×4 and true 20' 2×6. PT ground-contact species is whatever the yard carries (not our choice). Quantities are EXACT — 0% overage per the captain's decision: plan a follow-up run for shortages instead of padding the order. Saw kerf allowance used for stock packing: ⅛" per cut.

Framing and finish are TWO SEPARATE ORDERS. The finish lumber (siding, trim, doors, hardware) is modeled for real but ordered on a completely separate list — never mix the two. They are presented separately below, mirroring order_list.csv and order_list_finish.csv.

### 2.1 Framing order (order_list.csv)

Lumber | Treatment | Stock length | Qty | Notes
2×4 | KD (SPF #2) | 8' | 1 | Hingham Lumber
2×4 | KD (SPF #2) | 16' | 32 | yard stocks 16'; five 192" plates force 16' stock
2×6 | KD (SPF #2) | 10' | 15 | one each for the 13 rafters + 2 rake boards
2×6 | KD (SPF #2) | 20' | 2 | true 20' for the 18' fascia (yard stocks it)
2×6 | PT (ground contact) | 12' | 7 | floor joists, two 69" per board
2×6 | PT (ground contact) | 16' | 2 | rim joists
4×4 | PT (ground contact) | 16' | 2 | the two continuous skids
OSB ¾" | — | 4×8 sheet | 2 | subfloor; rip to 72" + 24" offcut (4 half-sheets used)

Stock packing (first-fit-decreasing, ⅛" kerf): 2×4 KD 1×8' + 32×16' = 520 LF (2.1% waste); 2×6 KD 15×10' + 2×20' = 190 LF (5.2%); 2×6 PT 7×12' + 2×16' = 116 LF (3.0%); 4×4 PT 2×16' = 32 LF (0%). Total framing dimensional lumber: 858 LF purchased. Per-board cut assignments are in CUT_LIST.md § "Stock-length order list".

### 2.2 Finish order (order_list_finish.csv) — SEPARATE ORDER

Lumber / item | Treatment | Stock length | Qty | Notes
1×10 | PRIMED | 12' | 1 | frieze (2× 61" side pieces)
1×10 | PRIMED | 16' | 2 | frieze (front/back, 181" each)
1×4 | KD | 8' | 1 | door rails
1×4 | KD | 14' | 5 | door stiles/rails
1×6 | KD | 14' | 15 | door planks (30 × 82¾")
1×6 | PRIMED | 8' | 3 | corner boards / casings
1×6 | PRIMED | 12' | 6 | corner boards / casings
1×6 | PRIMED | 14' | 3 | door casings
1×8 | PRIMED | 14' | 1 | siding (short pieces)
1×8 | PRIMED | 16' | 37 | siding + skirt
strap hinge 12" black | — | ea | 8 | hardware, line item only — 2 per leaf, 4 leaves
gate latch + hasp black | — | ea | 3 | hardware, line item only — 1 per opening (double: center latch)

Hardware has no geometry; it exists only as order line items. Finish stock packing totals: 1×10 44 LF, 1×4 78 LF, 1×6 KD 210 LF, 1×6 PRIMED 138 LF, 1×8 606 LF — 1,076 LF finish lumber purchased. Per-board assignments: CUT_LIST.md FINISH sections.

### 2.3 Foundation materials (not in either lumber order)

Per the captain's gravel-pocket drawings (inlined in Stage 1): 8 Tuff Blocks, 8 concrete pavers 16–18" (load spreaders), ¾" angular crushed stone (~1 yd³ for eight 24"×24"×8–12" pockets, placed in 3" lifts and tamped), landscape fabric, and shims (only where needed, never more than ½").

## 3. Step-by-step build guide

Work top to bottom: Stage 1 foundation/skids/floor → Stage 2 walls (front, back, left, right) → Stage 3 roof → Stage 4 finish. Every parts table lists model part names, counts and cut lengths exactly as they appear in CUT_LIST.md. Model coordinates: X along the 16' length, Y across the 6' width (front wall at low Y), Z up; deck top = z 0.

### Stage 1 — Foundation, skids, floor

#### Parts used (framing order)

Qty | Part (cut-list name) | Lumber | Cut length | Notes
2 | skid | 4×4 PT | 16' 0" (192") | continuous, no splices
2 | rim joist | 2×6 PT | 16' 0" (192") | front + back
14 | floor joist | 2×6 PT | 5' 9" (69") | 16" o.c. layout incl. one doubled pair
4 | sub floor osb | OSB ¾" half-sheet | 72" × 48" | rip two 4×8 sheets to 72" + 24"

Foundation materials (separate from the lumber orders): 8 Tuff Blocks, 8 pavers 16–18", ~1 yd³ ¾" crushed stone, landscape fabric, shims ≤ ½".

#### 1.1 Gravel pockets and blocks

Eight gravel pockets — four per skid line — carry the whole shed. Dig each pocket at least 24" square down to firm subsoil (depth varies; typically 8–12"), line with landscape fabric, fill with ¾" angular crushed stone in 3" lifts tamping each lift, set a concrete paver, then a Tuff Block. Set all eight block tops to ONE common plane with a string line, not individual level readings; shim only under ½". Keep pocket tops at or above finished grade and crown the grade away from the shed.

Fig. 2 — Gravel pocket + block layout, plan view. Adapted from the captain's drawing (gravel-pocket-plan-view.svg) for the current model: 16 ft × 6 ft footprint, two continuous 16 ft 4×4 skids (the old drawing's 8-ft sistered splice no longer applies), block centers 6" from each skid end at 5 ft o.c. (6", 5'-6", 10'-6", 15'-6") along each skid.

Fig. 3 — One gravel pocket, section detail (captain's drawing, inlined unchanged). Matches the model: 2×6 rim + floor joists bear on the 4×4 skid, skid on the block. Deck top ends up ~9¾" above the skid bottoms.

#### 1.2 Skids

1. Set the two 16' PT 4×4 skids on the block rows: the front skid under the front-wall bearing line, the back skid under the back-wall bearing line. Skid centerlines are 5' 8½" apart (68.5"); each skid is the full 192" shed length — ends land flush with the future rim joist ends (model x −3.5…188.5).
2. Each skid bears on four blocks, 6" in from each end and 5' apart (Fig. 2). Level and align the skids to the string-line plane; shim ≤ ½" only.
3. Check the rectangle: equal diagonals across the two skid lines before framing starts.

#### 1.3 Floor framing and decking

1. Nail the two 16' PT 2×6 rim joists flat-side out along the skid outsides (front rim y −3.5…−2, back rim y 67…68.5), bearing on the skids (rim bottoms at skid tops, z −6.25).
2. Set the 14 PT 2×6 floor joists at 69" between rims, on the layout below: first joist flush at the left end (x −3.5), then 16" o.c. (x 11, 27, 43, 59, 75, 91…), a doubled pair at x 91 + 92.5 (keeps the OSB seam and adds stiffness mid-span), 16" o.c. again (108.5, 124.5, 140.5, 156.5, 172.5), last joist flush at the right end (x 187).
3. Deck with the four ¾" OSB half-sheets (72" × 48"): sheet edges land on joists at x = 44.5, 92.5, 140.5; sheets run the full 72" width. Deck top is the build datum z = 0 — every wall measurement in the stages below starts here.

Fig. 4 — Floor framing plan. 14 PT 2×6 joists at 69": ends flush, 16" o.c. field, doubled pair at x 91/92.5. OSB seams land on joist centers.

### Stage 2 — Walls

Four wall assemblies, framed flat on the deck and stood in this order: front (tall, 123"), back, left, right — both side walls are the shed's rake walls (their double top plates and roof-edge studs carry the sloped roof line; the sloped rake plates themselves land in Stage 3). All wall lumber is 2×4 KD SPF #2. Deck top (z 0) is the reference plane for every height.

Sheathing: the model has NO separate wall sheathing — the 1×8 lap siding (Stage 4) is the wall surface, applied directly over the framing. If you want structural sheathing or a weather-resistive barrier, that is an addition outside the model and the order lists; the stages below assume the as-modeled build. Temporary diagonal bracing holds each wall plumb until the siding goes on.

### Stage 2A — Front wall (tall wall, door openings)

#### Parts used

Qty | Part | Cut length | Notes
1 | front wall bottom plate | 192" | full length
1 | front wall top plate | 192" | z 120–121.5
1 | front wall double top plate | 192" | z 121.5–123; runs the full width, ties both corners
1 | front wall king stud | 120" | left corner (x −3.5); as modeled it runs from the deck through the bottom plate
8 | front wall king studs | 118.5" | x 12.5, 53, 60.5, 76.5, 92.5, 96, 172.5, 187 (right corner)
2 | front wall jack studs | 84" | opening A (36") jacks at x 14 and 51.5, from the deck
2 | front wall jack studs | 82.5" | opening B (72") jacks at x 97.5 and 171, from the top of the plate
3 | front wall headers | 75" | opening B header: 2 flat 2×4s at the faces (z 84–87.5) + 1 flat ply capping them (z 87.5–89)
3 | front wall headers | 39" | opening A header, same 3-piece makeup
6 | front wall cripple studs | 31" | z 89–120 over the headers: x 28.5, 44.5 (A) and 108.5, 124.5, 140.5, 156.5 (B)

#### Assembly

1. Lay out the 192" bottom plate on the deck: mark stud/jack positions per the elevation below; the two rough openings are x 15.5…51.5 (36") and x 99…171 (72"), both with an 84" head.
2. Set the two 84" opening-A jacks from the deck (they run through the bottom plate as modeled; the sill segment between them is cut out after standing). Opening-B jacks (82.5") sit on top of the plate.
3. Kings at the 9 positions above; build each header as 2 flat 2×4s at the wall faces plus a capping flat ply — assembled depth 5" (z 84…89), resting on the jacks. Add the six 31" cripples over the headers.
4. Add the top plate (z 120) and the 192" double top plate (z 121.5) — wall stands 123" tall.
5. Stand the wall at the deck's front edge (outer face flush at y −3.5), plumb, and brace. Later walls tie into its double top plate at the corners.

Fig. 5 — Front wall (192" × 123"). Two openings: 36" and 72" wide, 84" heads. Headers are 2 flat face plies + 1 cap ply (5" deep, z 84…89); cripples fill 89…120.

### Stage 2B — Back wall

#### Parts used

Qty | Part | Cut length | Notes
1 | back wall bottom plate | 192" | full length
1 | back wall top plate | 192" | z 94.125–95.625
1 | back wall double top plate short | 185" | x 0…185; the 3½" corners are occupied by the side walls' double plates
13 | back wall studs | 92.625" (92⅝ pre-cut) | 16" o.c.: x −3.5, 11, 27, 43, 59, 75, 91, 107, 123, 139, 155, 171, 187

#### Assembly

1. Bottom plate full 192"; studs on the 16" layout above, all identical pre-cut 92⅝".
2. Top plate 192", then the 185" double top plate between the corner zones (side-wall double plates will cap the corners — the lap alternates).
3. Stand at the back edge (outer face y 68.5), plumb and brace. Wall height 97⅛".

Fig. 6 — Back wall (192" × 97⅛"). No openings. The double top plate is 185" — it stops 3½" short of each end where the left/right wall double plates tie the corners.

### Stage 2C — Left rake wall (rectangular part)

#### Parts used

Qty | Part | Cut length | Notes
1 | left side wall bottom plate | 65" | y 0…65 between front/back walls
1 | left wall top plate | 65" | z 94.125–95.625
1 | left wall double top plate | 68.5" | y 0…68.5 — runs over the back wall to tie the back corners
5 | left side wall studs | 92.625" (92⅝ pre-cut) | y 0, 15.5, 31.5, 47.5, 63.5 (16" o.c.)

#### Assembly

1. Bottom plate 65" between the front and back walls; five pre-cut studs at 16" o.c.
2. Top plate 65", then the 68.5" double top plate running the full width including over the back wall — this is what ties the back-left corner and later carries the left rake plate seat.
3. Stand on the deck's left edge (outer face x −3.5), plumb and brace; the sloped rake infill above comes in Stage 3.

### Stage 2D — Right rake wall (rectangular part + door opening)

#### Parts used

Qty | Part | Cut length | Notes
1 | right wall bottom plate long | 20.5" | y 44.5…65 (behind the opening)
1 | right wall bottom plate short | 8.5" | y 0…8.5 (in front of the opening)
1 | right wall top plate | 65" | z 94.125–95.625
1 | right wall double top plate | 68.5" | y 0…68.5, ties the back-right corner
5 | right wall studs | 92.625" (92⅝ pre-cut) | y 0, 5.5, 46, 55, 63.5
2 | right wall jack studs | 82.5" | y 7…8.5 and 44.5…46, from the top of the plate to the 84" head
3 | right wall headers | 39" | same 3-piece flat makeup as the front opening-A header (z 84…89)
2 | right wall cripple studs | 5.125" | y 19 and 32.5 over the header (z 89…94.125)

#### Assembly

1. The bottom plate is split by the door opening: 8.5" segment at the front end, 20.5" at the back — rough opening y 8.5…44.5 (36"), 84" head.
2. Studs per the layout; jacks on both sides of the opening; 39" header on the jacks; two short cripples over the header.
3. Top plate 65" + 68.5" double top plate as on the left wall; stand on the right edge (outer face x 188.5 — wall occupies x 185…188.5), plumb and brace.

Fig. 7 — Rake wall elevation (interior view). The rectangular wall (solid) is framed in Stages 2C/2D; the sloped rake plate and four stepped studs (dashed) land in Stage 3. Stepped stud lengths: 22.77", 16.96", 10.96", 4.96" — short enough to cut from scrap.

Standing order + tying the corners. Front wall first (its 192" double top plate runs full width), then back, left, right. Side-wall double plates (68.5") run over the back wall corners; the back wall's 185" double top plate fits between them. After all four are plumb and braced, the box is tied together at the plate line and ready for Stage 3.

### Stage 3 — Roof

Slope runs front (high, z 121.5 bearing at the front wall) to back (low, z 97⅛ at the back wall): 4.5 : 12 pitch (24.375 / 65, 20.56°). All roof lumber is 2×4/2×6 KD SPF #2. Every rafter is birdmouthed so it bears flat on BOTH double top plates — the model's verify gate checks the seat faces exist and nothing interpenetrates.

#### Parts used

Qty | Part | Lumber | Cut length | Notes
1 | left rake wall top plate | 2×4 | 69.42" (5' 9‑27/64) | sloped; top edge on the bearing line, plumb nose at the front, seat on the side DTP
1 | right rake wall top plate | 2×4 | 69.42" | same, right side
4 | left rake wall studs | 2×4 | 22.773 / 16.96 / 10.96 / 4.96" | stepped, tops mitred to the rake plate underside
4 | right rake wall studs | 2×4 | 22.773 / 16.96 / 10.96 / 4.96" | same, right side
13 | rafter | 2×6 | 115.344" (9' 7‑11/32) | 15⅞" o.c.; front + back birdsmouths, plumb tail cuts
1 | front fascia | 2×6 | 216" (18') | 12" past each side wall
1 | back fascia | 2×6 | 216" (18') | true 20' stock, cut to 18'
1 | left rake board | 2×6 | 115.344" | parallelogram, butts both fascia inner faces
1 | right rake board | 2×6 | 115.344" | same, right side

#### 3.1 Rake plates and rake studs

1. Each rake plate (69.42" 2×4 on edge) sits on the side wall's double top plate: its top edge IS the roof bearing line (121.5" at the front, falling 4.5" per foot to 97⅛" at the back), its back end seats flat on the back/left/right DTP top, and its front nose is trimmed plumb at the front wall inner face.
2. Set the four stepped studs per side on the DTP top (z 97⅛) at y 0, 15.5, 31.5, 47.5 — the same 16" layout as the wall below — with each top cut at the slope to meet the rake plate underside. Lengths: 22.77", 16.96", 10.96", 4.96" (cut from offcuts).

#### 3.2 Rafters with birdsmouth seats

1. Mark the rafter layout on the double top plates: 13 rafters at 15⅞" o.c., first at the left rake wall (x −3.5), last at the right rake wall (x 187).
2. Cut all 13 rafters identical from one pattern: front birdsmouth — flat seat on the front DTP top (z 123"), heel 4" outboard of the front wall inner face (y −4.0), plumb kick at the inner face; back birdsmouth — flat seat on the back DTP top (z 97⅛") across the plate width out to the back wall outer face (y 68.5), plumb kick there; plumb tail cuts at both ends (front tail 24" past the front wall face, back tail 12" past the back wall face).
3. Seat each rafter on both plates, toe-nail/screw through the plate. The rafter tops define the roof plane; tail tops land flush with the fascia tops (137‑11/16" front, 97‑3/16" back).

Fig. 8 — Birdsmouthed rafter profile exactly as modeled: front seat z 123" (heel y −4.0, 4" seat), back seat z 97⅛" (3½" across the plate), plumb kicks at the wall faces, plumb tails at y −27.5 / +80.5. The verify harness gates every seat face and the zero-interference sweep.

#### 3.3 Fascia and rake boards

1. Nail the two 18' 2×6 fascia to the rafter tails: front fascia at the front tails (z 132‑3/16…137‑11/16), back fascia at the back tails (z 91‑11/16…97‑3/16), each running x −15.5…200.5 — 12" past each side wall. Rafter tail tops come out flush with the fascia tops.
2. Fit the two rake boards (same 115.344" parallelogram as a rafter, no seats) along the left and right roof edges on the gable overhangs, butting the fascia inner faces.

Fig. 9 — Roof plan. 13 rafters at 15⅞" o.c. from x −3.5 to 187; front/back fascia 216"; rake boards on the gable overhangs. Front (top) is the high side.

#### 3.4 Sheathing and roofing

Not modeled. Roof sheathing, underlayment and roofing material are outside the model and both order lists. For reference: the slope between fascia inner faces runs 115.344" per side across 216", so plan sheet goods and drip edge accordingly, with the underlayment and fasteners your roofing spec calls for. Add these to a separate shopping list — they were deliberately excluded from the lumber orders.

### Stage 4 — Finish (siding, trim, doors)

All finish lumber is on the separate finish order: 1×8 PRIMED lap siding, PRIMED 1×6/1×10 trim, KD 1×4/1×6 doors; hardware is line items only. The model builds the finish in layers, each proud of the one behind: framing → siding (¾") → trim (¾") → door planks (¾") → door frames (¾"). Work in that order.

#### 4.1 Skirt boards (water table)

Qty | Part | Cut length | Notes
2 | finish skirt | 192" (1×8 PRIMED) | front + back, over the rim joist band
2 | finish skirt | 72" (1×8 PRIMED) | left + right

The skirt runs z −6.75…0.5 — it covers the rim joist face, and everything above starts from its top (z 0.5). The first siding course tucks in behind it.

#### 4.2 Lap siding (1×8 drop siding, 7" exposure)

Product: 1×8 drop siding (¾" × 7½" actual), 7" exposure; courses nest via a ½" × ⅜" rabbet/tongue so the wall stays in ONE plane. Courses start at the deck (behind the skirt) and run to: front wall z 123 (plate top), back wall tucked under the rafter tails, side walls up the rake line (rafter bottom + 1" tuck). Where the rake crosses a side course, that course is ripped/sloped to butt the course below — the frieze and casings cover the joints.

Wall | Courses / pieces | Cut lengths (model)
Back (no openings) | 14 | 14 × 192"
Front | 6 + 12 + 12 + 12 | 6 × 192" full width above the 84" heads; below the heads, 12 courses break into piers: 12 × 19" (left of opening A), 12 × 47.5" (between openings), 12 × 17.5" (right of opening B)
Left | 14 + 4 | 14 × 72" full courses; 4 rake-cut tops: 66.167", 46.167", 26.167", 6.167"
Right (has the door) | 1 + 13 + 13 + 4 | 1 × 72" full course at the 84" line; below the head each of 13 courses splits into a 24" pier (back of the door) + 12" pier (front of the door); 4 rake-cut tops as on the left

#### 4.3 Trim (corners, frieze, casings)

Qty | Part | Cut length | Notes
8 | finish corner boards | 2×123.313", 2×122.5", 2×96.313", 2×94.75" (1×6) | two per corner, one flat on each wall face, from the skirt top (z 0.5) to the frieze/rake line — the long pair at the front corners, the short pair at the back
2 | finish frieze | 181" (1×10) | front + back bands under the eaves, between the corner boards; front: z 113.75…123
2 | finish frieze | 61" (1×10) | left + right, raked along the roof line
6 | finish door casings | 83.5" (1×6) | jamb casings, two per opening, z 0.5…84
1 | finish door casings | 83" (1×6) | head casing over the 72" opening (spans the jambs)
2 | finish door casings | 47" (1×6) | head casings over the two 36" openings

Trim is one proud layer OUTSIDE the siding (backs touching the siding face); install skirt → siding → corners → frieze → casings in that order.

#### 4.4 Board-and-batten doors

Four leaves over the three openings: one single over the front 36", a center double over the front 72", one single over the right-wall 36". Each leaf = vertical 1×6 planks edge-to-edge with a 1×4 perimeter frame (stiles + rails) on the outer face, hung one layer proud of the casing face where the strap hinges bear. Leaf bottoms at z 1 (just above the skirt top), tops at z 83.75 — ¼" below the 84" heads. Each leaf overlaps its jamb casings by 1½" per side.

Qty | Part | Cut length | Notes
30 | finish door planks | 82.75" (1×6 KD) | 8 planks per single leaf (rip to 4.875" each), 7 per double leaf (rip to 5.339")
8 | finish door stiles (rails) | 82.75" (1×4 KD) | two per leaf, full leaf height
4 | finish door rails | 32" (1×4 KD) | top + bottom rails of the two single leaves (39" leaves − 2×3½" stiles)
4 | finish door rails | 30.375" (1×4 KD) | top + bottom rails of each double leaf (37.375" leaves − stiles)
8 | strap hinge 12" black | — | hardware: 2 per leaf, 4 leaves
3 | gate latch + hasp black | — | hardware: 1 per opening (double door: center latch)

Fig. 10 — Plan view through a door jamb (36" opening A, cut at z = 40"), with the left jamb zoomed to show the four ¾" steps: 1×8 lap siding on the wall plane (y −3.5…−4.25), 1×6 jamb casing on the siding face (−4.25…−5.0), door planks on the casing face (−5.0…−5.75), 1×4 leaf frame outboard (−5.75…−6.5) — 3" proud of the wall face in total. Siding and casing stop at the clear opening; the leaf laps each jamb casing 1½". All layer planes verified seated by cad.verify.

Fig. 11 — One single leaf (the front-left and right-wall doors are identical): 8 vertical 1×6 planks ripped to 4.875", 1×4 stiles full height, rails top and bottom, hinges on the rails into the casing face. The double leaves are 37.375" wide (7 planks @ 5.339") with a ¼" meeting gap.

## 4. Cut list reference

Complete framing cut list, grouped exactly like CUT_LIST.md (actual dimensions, no kerf; the stock-length packing that turns these into the order quantities of §2 lives in CUT_LIST.md § "Stock-length order list"). Finish cuts are in the Stage 4 tables above and in the FINISH sections of CUT_LIST.md.

### Skids

Qty | Lumber | Treatment | Length | Name
2 | 4×4 | PT | 192" | skid

### Floor

Qty | Lumber | Treatment | Length | Name
2 | 2×6 | PT | 192" | rim joist
14 | 2×6 | PT | 69" | floor joist
4 | OSB ¾" (half sheets) | — | 72" × 48" | sub floor osb

### Back wall

Qty | Lumber | Treatment | Length | Name
1 | 2×4 | KD | 192" | back wall bottom plate
1 | 2×4 | KD | 192" | back wall top plate
1 | 2×4 | KD | 185" | back wall double top plate short
13 | 2×4 | KD | 92.625" | back wall studs

### Front wall

Qty | Lumber | Treatment | Length | Name
1 | 2×4 | KD | 192" | front wall bottom plate
1 | 2×4 | KD | 192" | front wall top plate
1 | 2×4 | KD | 192" | front wall double top plate
1 | 2×4 | KD | 120" | front wall king studs
8 | 2×4 | KD | 118.5" | front wall king studs
2 | 2×4 | KD | 84" | front wall jack studs
2 | 2×4 | KD | 82.5" | front wall jack studs
3 | 2×4 | KD | 75" | front wall headers
3 | 2×4 | KD | 39" | front wall headers
6 | 2×4 | KD | 31" | front wall cripple studs

### Left wall

Qty | Lumber | Treatment | Length | Name
5 | 2×4 | KD | 92.625" | left side wall studs
1 | 2×4 | KD | 68.5" | left wall double top plate
1 | 2×4 | KD | 65" | left side wall bottom plate
1 | 2×4 | KD | 65" | left wall top plate

### Right wall

Qty | Lumber | Treatment | Length | Name
5 | 2×4 | KD | 92.625" | right wall studs
2 | 2×4 | KD | 82.5" | right wall jack studs
1 | 2×4 | KD | 68.5" | right wall double top plate
1 | 2×4 | KD | 65" | right wall top plate
3 | 2×4 | KD | 39" | right wall headers
1 | 2×4 | KD | 20.5" | right wall bottom plate long
1 | 2×4 | KD | 8.5" | right wall bottom plate short
2 | 2×4 | KD | 5.125" | right wall cripple studs

### Left / right rake walls

Qty | Lumber | Treatment | Length | Name
1 | 2×4 | KD | 69.42" | left rake wall top plate
1 | 2×4 | KD | 22.773" | left rake wall studs
1 | 2×4 | KD | 16.96" | left rake wall studs
1 | 2×4 | KD | 10.96" | left rake wall studs
1 | 2×4 | KD | 4.96" | left rake wall studs
1 | 2×4 | KD | 69.42" | right rake wall top plate
1 | 2×4 | KD | 22.773" | right rake wall studs
1 | 2×4 | KD | 16.96" | right rake wall studs
1 | 2×4 | KD | 10.96" | right rake wall studs
1 | 2×4 | KD | 4.96" | right rake wall studs

### Roof

Qty | Lumber | Treatment | Length | Name
1 | 2×6 | KD | 216" | back fascia
1 | 2×6 | KD | 216" | front fascia
1 | 2×6 | KD | 115.344" | left rake board
13 | 2×6 | KD | 115.344" | rafter
1 | 2×6 | KD | 115.344" | right rake board

## 5. Sources, verification, known quirks

- Geometry authority: repo woodbike-shed at commit c86e75d (current main): cad/*.py (build123d model — framing, siding, trim, doors; shared layout math in cad/common.py) plus the generated CUT_LIST.md, order_list.csv, order_list_finish.csv.
- Verification run (2026-08-11): ~/.venvs/woodbike-shed/bin/python -m cad.verify → OK: 293 parts (117 framing, 176 finish), 36 framing cut-list names; dims/volumes/placements match audit data; seats/kicks/ends flush; finish layers seated; 0 unallowed interference (333 pairs swept). The harness checks every part's dims/volume/placement against the audit data, gates the rafter birdsmouth seat/kick faces, rake-stud mitres, tail-flush-with-fascia, finish layer planes, and runs a full pairwise interference sweep.
- Model viewing: view.py (OCP CAD Viewer, part tree mirrors the cut list); blender/build_scene.py renders (--skin for the dressed variant).
- Design decisions (context only — all resolved, none re-opened): data/woodbike-shed-design-calls-decisions.md — 92⅝" pre-cut studs, keep 16' 2×4, true 20' 2×6 fascia, exact quantities, SPF #2 KD, separate finish order, two continuous 16' 4×4 skids (no sistering), PT ground-contact species = yard stock, Onshape sync deferred.
- Known intentional quirks (as modeled, carried from the captain's Onshape build): the two opening-A jack studs (84") and one front king stud (120") run from the deck THROUGH the front bottom plate — documented modeling quirk, exempt from the interference sweep. The inner volume reference envelope pre-dates the roof and is excluded from all lists.
- Deliberate divergence from Onshape: the Onshape document still carries the pre-decision geometry (93" studs, sistered skids, no birdmouths/finish). It is a retired record copy — do not sync from it.
- Foundation drawings: captain's gravel-pocket set at personal/woodbike-shed/gravel/files/ (read-only originals). The plan view in Fig. 2 is adapted from them for the 16' footprint and continuous skids; the section detail (Fig. 3) is inlined unchanged.
- Not modeled (builder scope): wall sheathing/WRB (Stage 2 note), roof sheathing/underlayment/roofing (Stage 3.4), fasteners, paint/caulk for the primed finish stock, door stops/weatherstrip.

Definition of done for this document: it replaces the Onshape-era report (archived as report.2026-08-08.onshape.html), every dimension and count traces to the landed model code or its generated cut lists, framing and finish orders stay separate, and the stages read top to bottom: skids/floor → each wall → roof → finish.

Generated 2026-08-11 by a firstmate scout task (woodbike-shed-build-guide) from the landed model at commit c86e75d. Self-contained: no external assets; renders standalone from file://.
