griswaldbrooks/woodbike-shed/docs/_layouts/guide.html

--- layout: default --- {%- comment -%} Layout for one guide page. The guide pages carry their own H1 and content; this layout adds the stage bar on top and the prev/next pager below. page.prev / page.next are .md filenames of sibling guide pages (see each page's front matter). URLs are derived directly from those filenames so the pager keeps working exactly as the PDF build's canonical reading order does. {%- endcomment -%} {%- if page.prev == "index.md" -%} {%- assign prev_url = "/guide/" -%} {%- elsif page.prev -%} {%- assign prev_url = page.prev | replace: ".md", ".html" | prepend: "/guide/" -%} {%- endif -%} {%- if page.next == "index.md" -%} {%- assign next_url = "/guide/" -%} {%- elsif page.next -%} {%- assign next_url = page.next | replace: ".md", ".html" | prepend: "/guide/" -%} {%- endif -%} {%- if prev_url -%} {%- assign prev_page = site.pages | where: "url", prev_url | first -%} {%- endif -%} {%- if next_url -%} {%- assign next_page = site.pages | where: "url", next_url | first -%} {%- endif -%}

{{ site.title | escape }} {%- if page.stage %}{{ page.stage | escape }}{% endif -%}

{{ content }}
